xjtuecho/EBAZ4205/HW/ebaz4205/kicad/IO.kicad_sch

## KiCad design HW/ebaz4205/kicad/IO.kicad_sch (2021-02-16)

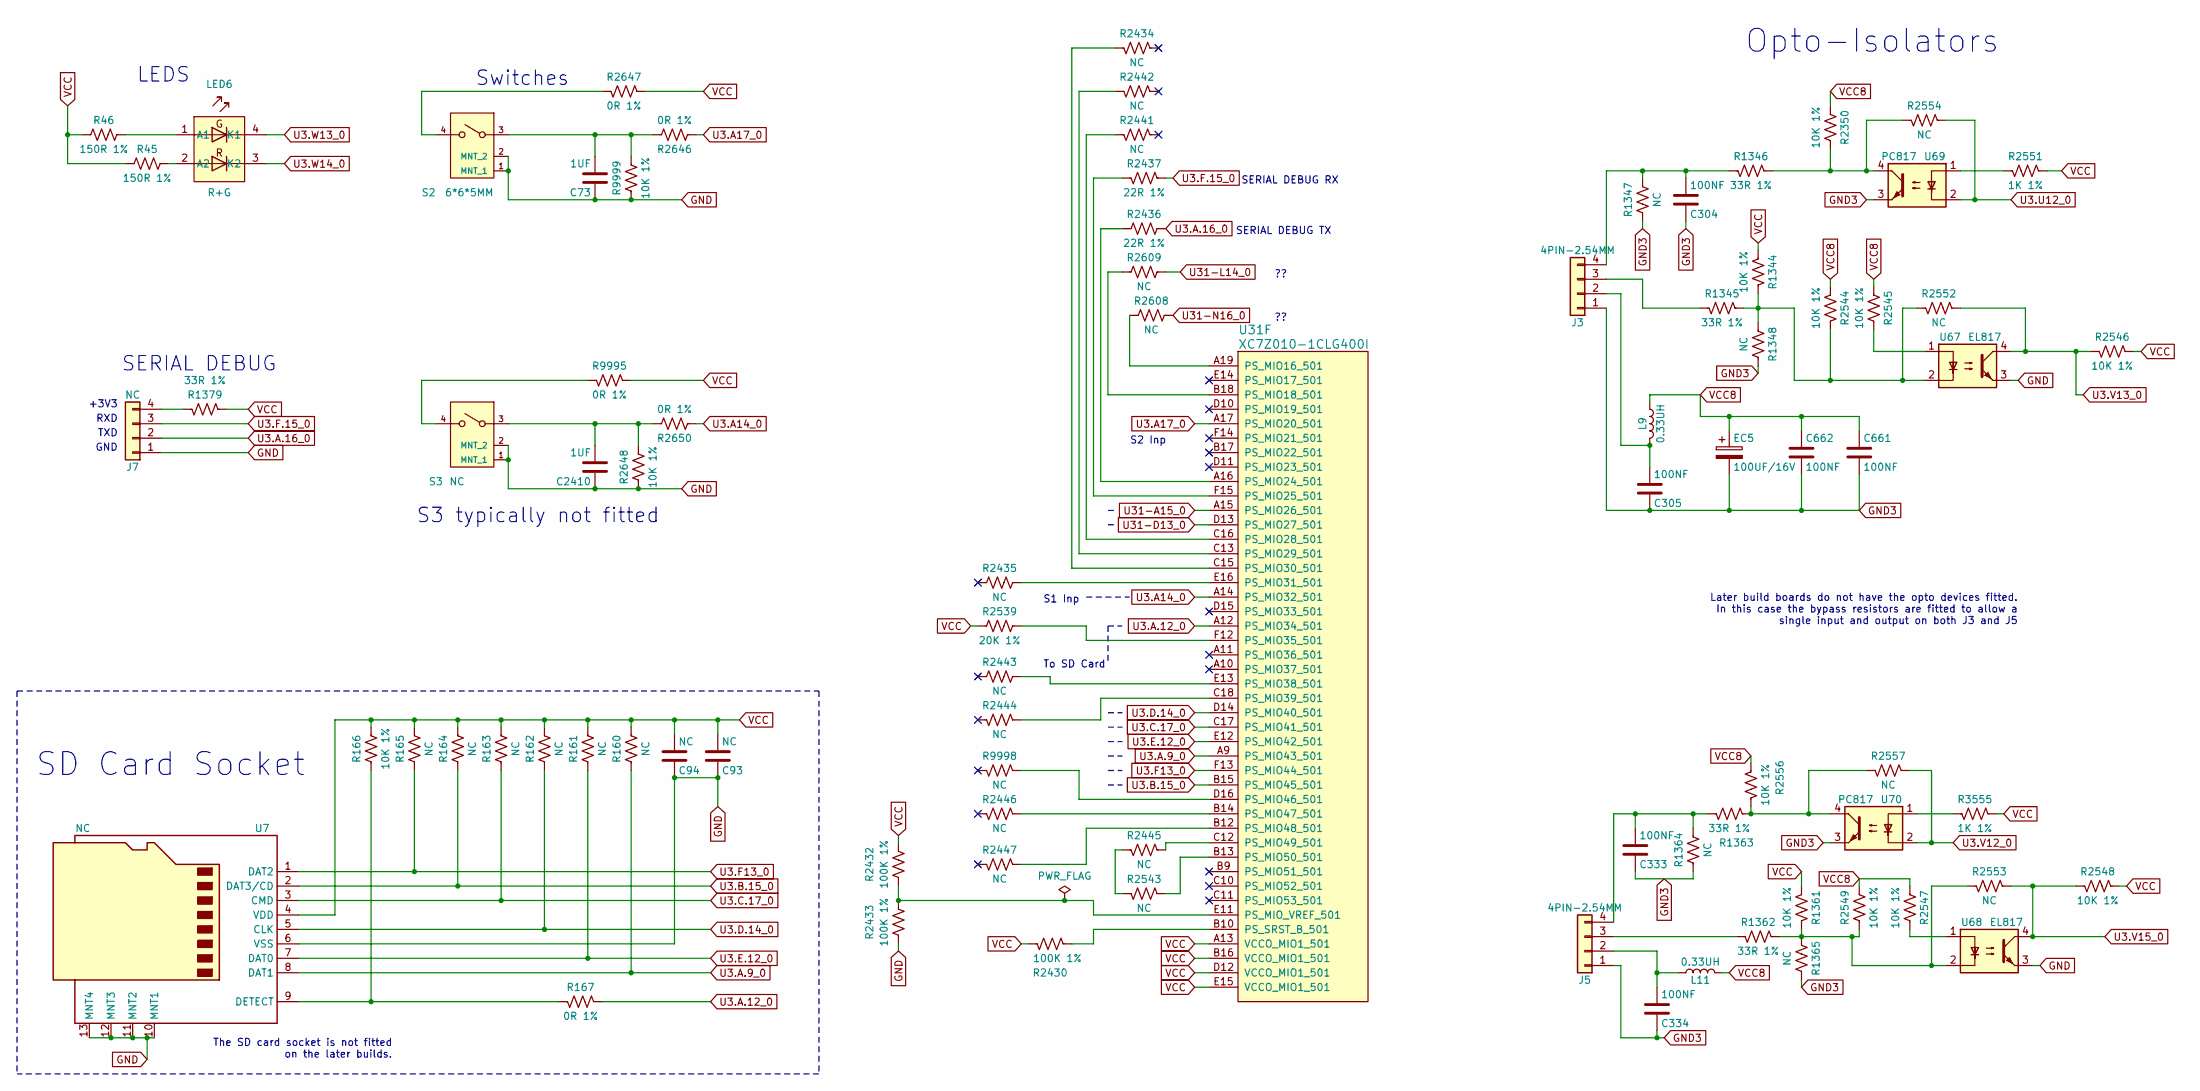
[picture p15: schematic IO.kicad_sch]

Parts:
C73, C2410: 1UF
C93, C94: NC
C304, C305, C333, C334, C661, C662: 100NF
EC5: 100UF/16V
J3, J5: 4PIN-2.54MM
J7: NC
L9, L11: 0.33UH
LED6: R+G
R45, R46: 150R 1%
R160, R161, R162, R163, R164, R165, R1347, R1348, R1364, R1365, R2434, R2435, R2441, R2442, R2443, R2444, R2445, R2446, R2447, R2543, R2552, R2553, R2554, R2557, R2608, R2609, R9998: NC
R166, R1344, R1361, R2350, R2544, R2545, R2546, R2547, R2548, R2549, R2556, R2648, R9999: 10K 1%
R167, R2646, R2647, R2650, R9995: 0R 1%
R1345, R1346, R1362, R1363, R1379: 33R 1%
R2430, R2432, R2433: 100K 1%
R2436, R2437: 22R 1%
R2539: 20K 1%
R2551, R3555: 1K 1%
S2: 6*6*5MM; voltage rating DC 24V; mouser part number 506-FSMRACD; digikey description SWITCH TACTILE SPST-NO 0.05A 24V
S3: NC; voltage rating DC 24V; mouser part number 506-FSMRACD; digikey description SWITCH TACTILE SPST-NO 0.05A 24V
U7: NC
U31: XC7Z010-1CLG400I
U67, U68: EL817
U69, U70: PC817

Connections:
GND: C73.1, C93.1, C94.1, C2410.1, J7.1, R2433.2, R2648.1, R9999.1, S2.1 (MNT_1), S2.2 (MNT_2), S3.1 (MNT_1), S3.2 (MNT_2), U7.6 (VSS), U7.10 (MNT1), U7.11 (MNT2), U7.12 (MNT3), U7.13 (MNT4), U67.3, U68.3
GND3: C304.1, C305.1, C333.1, C334.1, C661.1, C662.2, EC5.2, J3.1, J5.1, R1347.1, R1348.2, R1364.1, R1365.2, U69.3, U70.3
unnamed: C73.2, R2646.2, R9999.2, S2.3
unnamed: C304.2, J3.4, R1346.2, R1347.2
unnamed: C305.2, J3.2, L9.1
unnamed: C333.2, J5.4, R1363.2, R1364.2
unnamed: C334.2, J5.2, L11.1
unnamed: C2410.2, R2648.2, R2650.2, S3.3
unnamed: J3.3, R1345.2
unnamed: J5.3, R1362.2
unnamed: J7.4, R1379.2
unnamed: LED6.1 (A1), R46.2
unnamed: LED6.2 (A2), R45.2
unnamed: R166.1, R167.2, U7.9 (DETECT)
unnamed: R1344.1, R1345.1, R1348.1, R2544.1, R2552.2, U67.2
unnamed: R1346.1, R2350.2, R2554.2, U69.4
unnamed: R1361.1, R1362.1, R1365.1, R2549.1, R2553.2, U68.2
unnamed: R1363.1, R2556.2, R2557.2, U70.4
unnamed: R2430.1, U31.B10 (PS_SRST_B_501)
unnamed: R2432.1, R2433.1, U31.E11 (PS_MIO_VREF_501)
unnamed: R2434.2, U31.C15 (PS_MIO30_501)
unnamed: R2435.2, U31.E16 (PS_MIO31_501)
unnamed: R2436.1, U31.A16 (PS_MIO24_501)
unnamed: R2437.2, U31.F15 (PS_MIO25_501)
unnamed: R2441.2, U31.C16 (PS_MIO28_501)
unnamed: R2442.2, U31.C13 (PS_MIO29_501)
unnamed: R2443.2, U31.E13 (PS_MIO38_501)
unnamed: R2444.1, U31.C18 (PS_MIO39_501)
unnamed: R2445.1, U31.C12 (PS_MIO49_501)
unnamed: R2445.2, R2543.2
unnamed: R2446.1, U31.B14 (PS_MIO47_501)
unnamed: R2447.1, U31.B12 (PS_MIO48_501)
unnamed: R2539.2, U31.F12 (PS_MIO35_501)
unnamed: R2543.1, U31.B13 (PS_MIO50_501)
unnamed: R2545.2, U67.1
unnamed: R2547.2, U68.1
unnamed: R2551.2, U69.1
unnamed: R2608.1, U31.A19 (PS_MIO16_501)
unnamed: R2609.1, U31.B18 (PS_MIO18_501)
unnamed: R2647.2, S2.4
unnamed: R3555.2, U70.1
unnamed: R9995.2, S3.4
unnamed: R9998.1, U31.D16 (PS_MIO46_501)
U3.A14_0: R2650.1, U31.A14 (PS_MIO32_501)
U3.A17_0: R2646.1, U31.A17 (PS_MIO20_501)
U3.A.9_0: R160.1, U7.8 (DAT1), U31.A9 (PS_MIO43_501)
U3.A.12_0: R167.1, U31.A12 (PS_MIO34_501)
U3.A.16_0: J7.2, R2436.2
U3.B.15_0: R164.1, U7.2 (DAT3/CD), U31.B15 (PS_MIO45_501)
U3.C.17_0: R163.1, U7.3 (CMD), U31.C17 (PS_MIO41_501)
U3.D.14_0: R162.1, U7.5 (CLK), U31.D14 (PS_MIO40_501)
U3.E.12_0: R161.1, U7.7 (DAT0), U31.E12 (PS_MIO42_501)
U3.F13_0: R165.1, U7.1 (DAT2), U31.F13 (PS_MIO44_501)
U3.F.15_0: J7.3, R2437.1
U3.U12_0: R2554.1, U69.2
U3.V12_0: R2557.1, U70.2
U3.V13_0: R2546.2, R2552.1, U67.4
U3.V15_0: R2548.2, R2553.1, U68.4
U3.W13_0: LED6.4 (K1)
U3.W14_0: LED6.3 (K2)
U31-A15_0: U31.A15 (PS_MIO26_501)
U31-D13_0: U31.D13 (PS_MIO27_501)
U31-L14_0: R2609.2
U31-N16_0: R2608.2
VCC: C93.2, C94.2, R45.1, R46.1, R160.2, R161.2, R162.2, R163.2, R164.2, R165.2, R166.2, R1344.2, R1361.2, R1379.1, R2430.2, R2432.2, R2539.1, R2546.1, R2548.1, R2551.1, R2647.1, R3555.1, R9995.1, U7.4 (VDD), U31.A13 (VCCO_MIO1_501), U31.B16 (VCCO_MIO1_501), U31.D12 (VCCO_MIO1_501), U31.E15 (VCCO_MIO1_501)
VCC8: C661.2, C662.1, EC5.1, L9.2, L11.2, R2350.1, R2544.2, R2545.1, R2547.1, R2549.2, R2556.1

Notes on the sheet:
SD Card Socket
+3V3
RXD
TXD
GND
LEDS
SERIAL DEBUG
The SD card socket is not fitted on the later builds.
Switches
S3 typically not fitted
S1 Inp
To SD Card
S2 Inp
SERIAL DEBUG TX
SERIAL DEBUG RX
Opto-Isolators
Later build boards do not have the opto devices fitted. In this case the bypass resistors are fitted to allow a single input and output on both J3 and J5
