xjtuecho/EBAZ4205/HW/ebaz4205/kicad/Mem_Zynq.kicad_sch

## KiCad design HW/ebaz4205/kicad/Mem_Zynq.kicad_sch (2021-02-16)

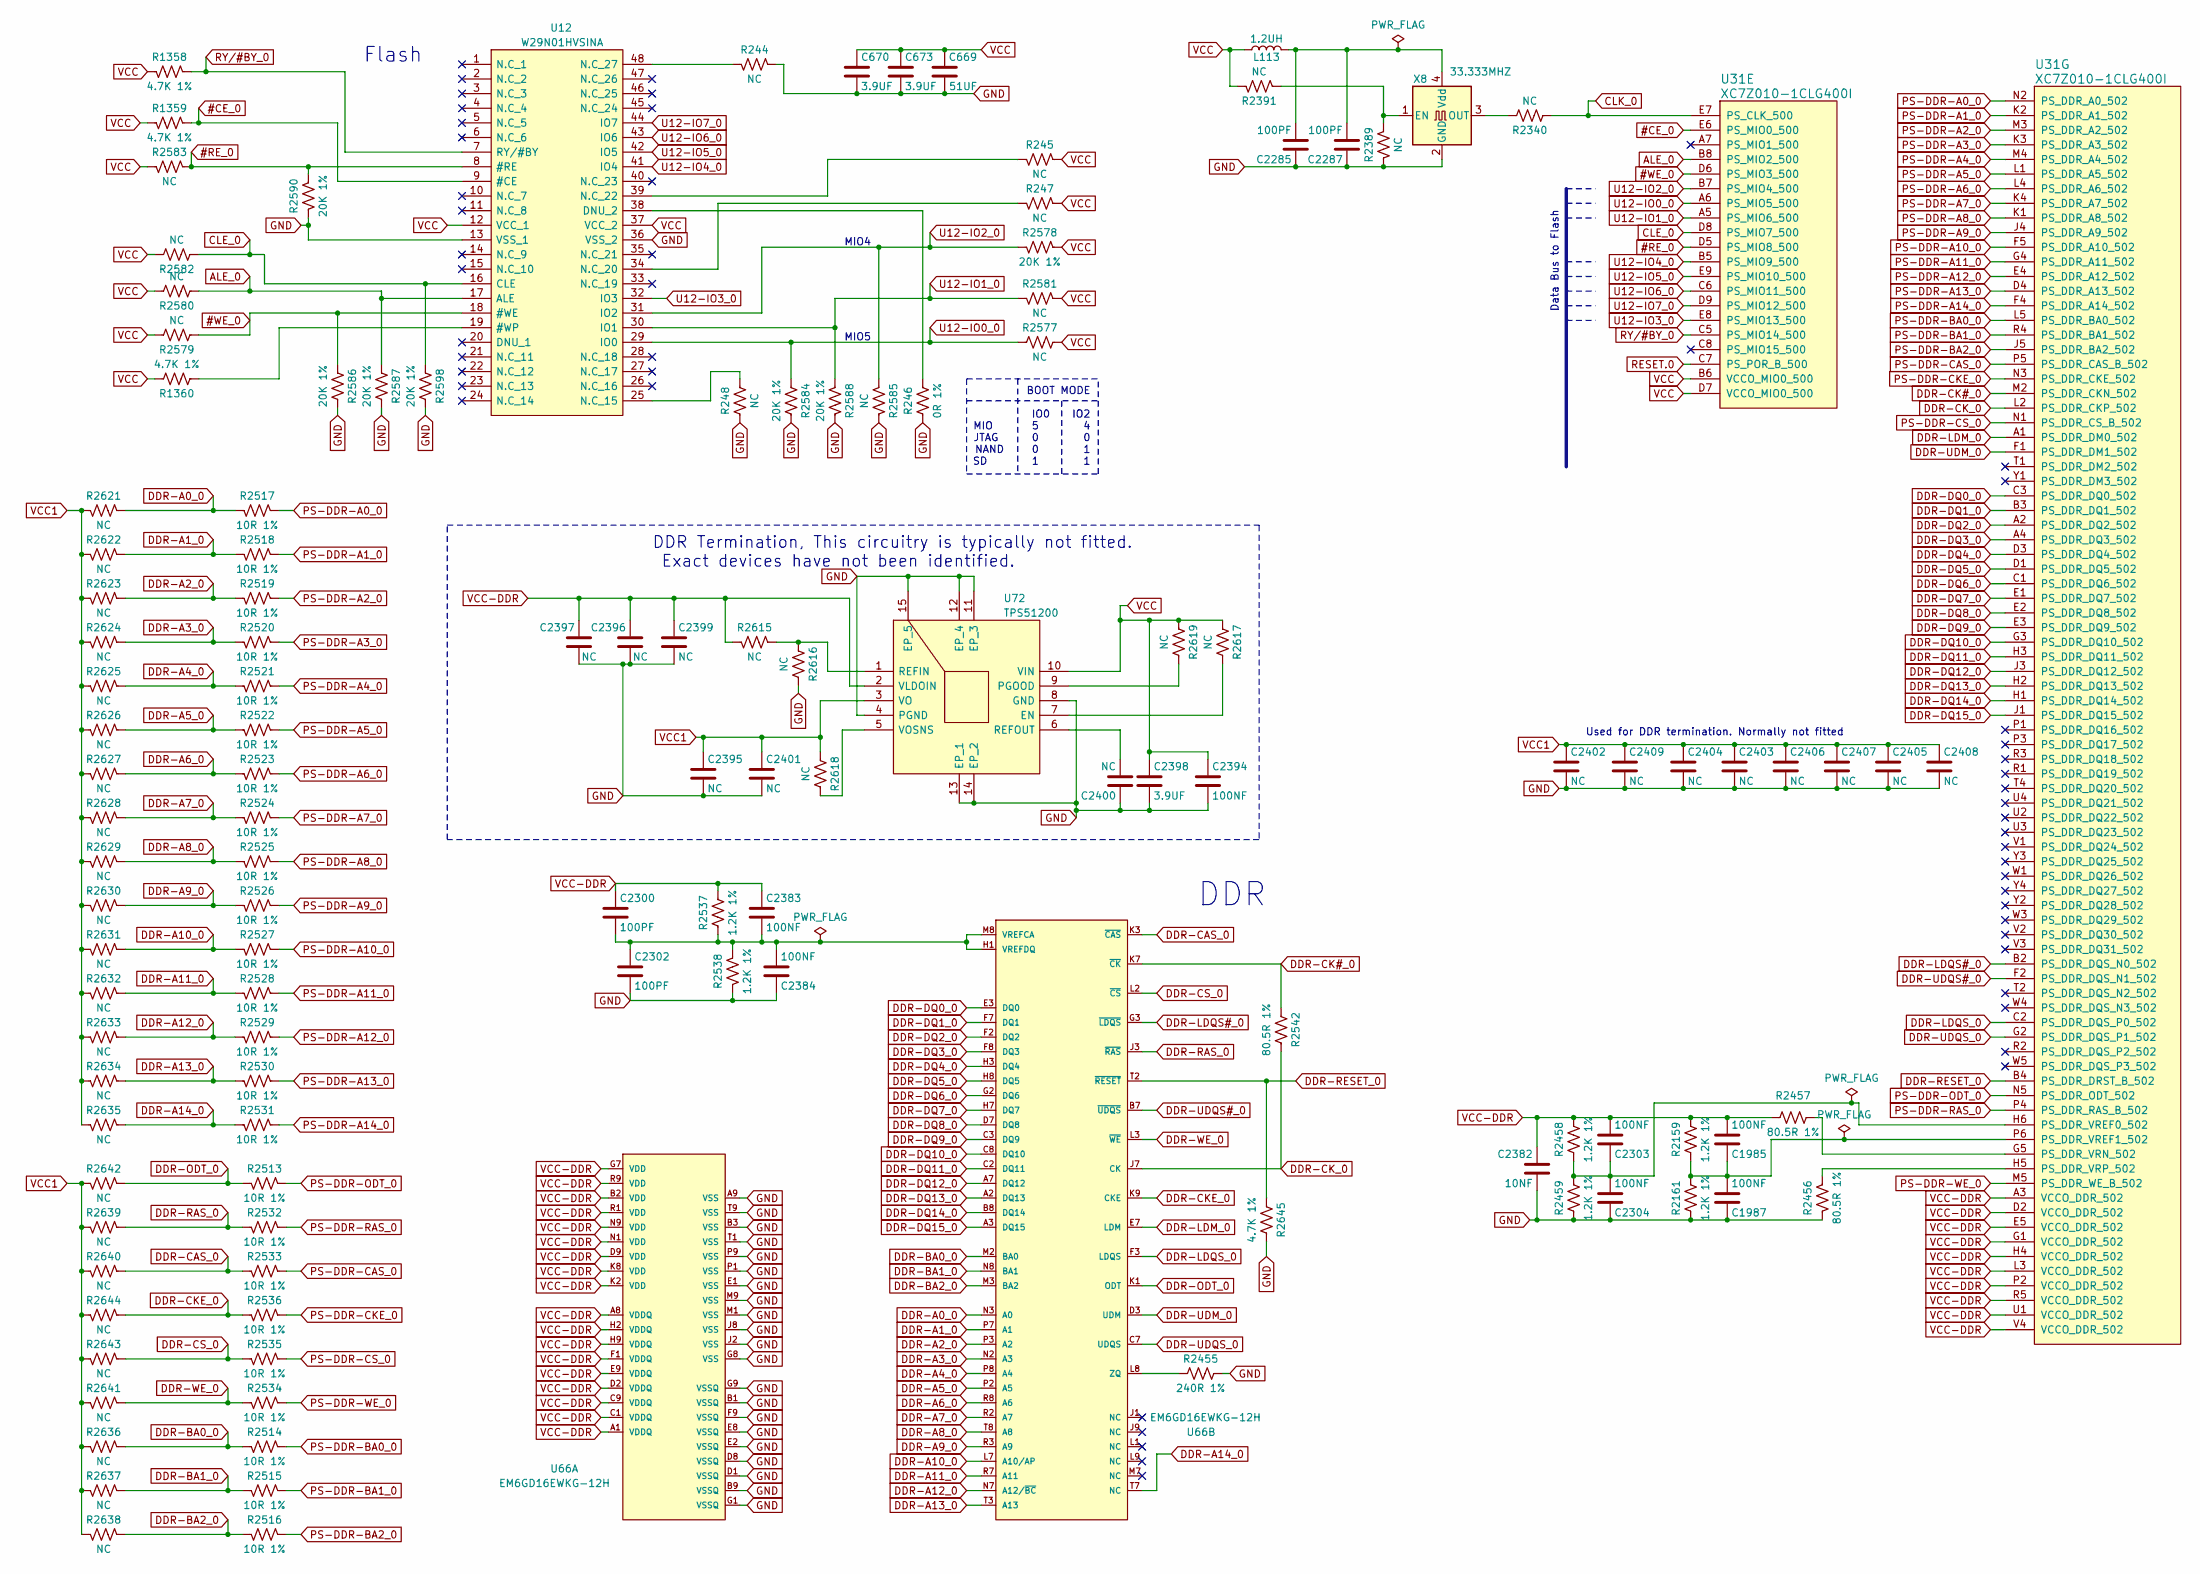
[picture p16: schematic Mem_Zynq.kicad_sch]

Parts:
C669: 51UF
C670, C673, C2398: 3.9UF
C1985, C1987, C2303, C2304, C2383, C2384, C2394: 100NF
C2285, C2287, C2300, C2302: 100PF
C2382: 10NF
C2395, C2396, C2397, C2399, C2400, C2401, C2402, C2403, C2404, C2405, C2406, C2407, C2408, C2409: NC
L113: 1.2UH
R244, R245, R247, R248, R2340, R2389, R2391, R2577, R2579, R2580, R2581, R2582, R2583, R2585, R2615, R2616, R2617, R2618, R2619, R2621, R2622, R2623, R2624, R2625, R2626, R2627, R2628, R2629, R2630, R2631, R2632, R2633, R2634, R2635, R2636, R2637, R2638, R2639, R2640, R2641, R2642, R2643, R2644: NC
R246: 0R 1%
R1358, R1359, R1360, R2645: 4.7K 1%
R2159, R2161, R2458, R2459, R2537, R2538: 1.2K 1%
R2455: 240R 1%
R2456, R2457, R2542: 80.5R 1%
R2513, R2514, R2515, R2516, R2517, R2518, R2519, R2520, R2521, R2522, R2523, R2524, R2525, R2526, R2527, R2528, R2529, R2530, R2531, R2532, R2533, R2534, R2535, R2536: 10R 1%
R2578, R2584, R2586, R2587, R2588, R2590, R2598: 20K 1%
U12: W29N01HVSINA; SOP50P2000X120-48N; Manufacturer_Part_Number W29N01HVSINA; Mouser Part Number 454-W29N01HVSINA
U31: XC7Z010-1CLG400I
U66: EM6GD16EWKG-12H; mouser part number 340-135814-TRAY; digikey description IC DRAM 2G PARALLEL 96FBGA
U72: TPS51200; Manufacturer_Part_Number TPS51200AQDRCRQ1; Mouser Part Number 595-TPS51200AQDRCRQ1
X8: 33.333MHZ

Connections:
#CE_0: R1359.1, U12.9 (#CE), U31.E6 (PS_MIO0_500)
#RE_0: R2583.1, R2590.1, U12.8 (#RE), U31.D5 (PS_MIO8_500)
#WE_0: R2579.1, R2586.1, U12.18 (#WE), U31.D6 (PS_MIO3_500)
ALE_0: R2580.1, R2587.1, U12.17 (ALE), U31.B8 (PS_MIO2_500)
CLE_0: R2582.1, R2598.1, U12.16 (CLE), U31.D8 (PS_MIO7_500)
CLK_0: R2340.1, U31.E7 (PS_CLK_500)
DDR-A0_0: R2517.2, R2621.1, U66.N3 (A0)
DDR-A1_0: R2518.2, R2622.1, U66.P7 (A1)
DDR-A2_0: R2519.2, R2623.1, U66.P3 (A2)
DDR-A3_0: R2520.2, R2624.1, U66.N2 (A3)
DDR-A4_0: R2521.2, R2625.1, U66.P8 (A4)
DDR-A5_0: R2522.2, R2626.1, U66.P2 (A5)
DDR-A6_0: R2523.2, R2627.1, U66.R8 (A6)
DDR-A7_0: R2524.2, R2628.1, U66.R2 (A7)
DDR-A8_0: R2525.2, R2629.1, U66.T8 (A8)
DDR-A9_0: R2526.2, R2630.1, U66.R3 (A9)
DDR-A10_0: R2527.2, R2631.1, U66.L7 (A10/AP)
DDR-A11_0: R2528.2, R2632.1, U66.R7 (A11)
DDR-A12_0: R2529.2, R2633.1, U66.N7 (A12/~BC~)
DDR-A13_0: R2530.2, R2634.1, U66.T3 (A13)
DDR-A14_0: R2531.2, R2635.1, U66.T7 (NC)
DDR-BA0_0: R2514.2, R2636.1, U66.M2 (BA0)
DDR-BA1_0: R2515.2, R2637.1, U66.N8 (BA1)
DDR-BA2_0: R2516.2, R2638.1, U66.M3 (BA2)
DDR-CAS_0: R2533.2, R2640.1, U66.K3 (~CAS~)
DDR-CK#_0: R2542.1, U31.M2 (PS_DDR_CKN_502), U66.K7 (~CK~)
DDR-CKE_0: R2536.2, R2644.1, U66.K9 (CKE)
DDR-CK_0: R2542.2, U31.L2 (PS_DDR_CKP_502), U66.J7 (CK)
DDR-CS_0: R2535.2, R2643.1, U66.L2 (~CS~)
DDR-DQ0_0: U31.C3 (PS_DDR_DQ0_502), U66.E3 (DQ0)
DDR-DQ1_0: U31.B3 (PS_DDR_DQ1_502), U66.F7 (DQ1)
DDR-DQ2_0: U31.A2 (PS_DDR_DQ2_502), U66.F2 (DQ2)
DDR-DQ3_0: U31.A4 (PS_DDR_DQ3_502), U66.F8 (DQ3)
DDR-DQ4_0: U31.D3 (PS_DDR_DQ4_502), U66.H3 (DQ4)
DDR-DQ5_0: U31.D1 (PS_DDR_DQ5_502), U66.H8 (DQ5)
DDR-DQ6_0: U31.C1 (PS_DDR_DQ6_502), U66.G2 (DQ6)
DDR-DQ7_0: U31.E1 (PS_DDR_DQ7_502), U66.H7 (DQ7)
DDR-DQ8_0: U31.E2 (PS_DDR_DQ8_502), U66.D7 (DQ8)
DDR-DQ9_0: U31.E3 (PS_DDR_DQ9_502), U66.C3 (DQ9)
DDR-DQ10_0: U31.G3 (PS_DDR_DQ10_502), U66.C8 (DQ10)
DDR-DQ11_0: U31.H3 (PS_DDR_DQ11_502), U66.C2 (DQ11)
DDR-DQ12_0: U31.J3 (PS_DDR_DQ12_502), U66.A7 (DQ12)
DDR-DQ13_0: U31.H2 (PS_DDR_DQ13_502), U66.A2 (DQ13)
DDR-DQ14_0: U31.H1 (PS_DDR_DQ14_502), U66.B8 (DQ14)
DDR-DQ15_0: U31.J1 (PS_DDR_DQ15_502), U66.A3 (DQ15)
DDR-LDM_0: U31.A1 (PS_DDR_DM0_502), U66.E7 (LDM)
DDR-LDQS#_0: U31.B2 (PS_DDR_DQS_N0_502), U66.G3 (~LDQS~)
DDR-LDQS_0: U31.C2 (PS_DDR_DQS_P0_502), U66.F3 (LDQS)
DDR-ODT_0: R2513.2, R2642.1, U66.K1 (ODT)
DDR-RAS_0: R2532.2, R2639.1, U66.J3 (~RAS~)
DDR-RESET_0: R2645.1, U31.B4 (PS_DDR_DRST_B_502), U66.T2 (~RESET~)
DDR-UDM_0: U31.F1 (PS_DDR_DM1_502), U66.D3 (UDM)
DDR-UDQS#_0: U31.F2 (PS_DDR_DQS_N1_502), U66.B7 (~UDQS~)
DDR-UDQS_0: U31.G2 (PS_DDR_DQS_P1_502), U66.C7 (UDQS)
DDR-WE_0: R2534.2, R2641.1, U66.L3 (~WE~)
GND: C669.1, C670.2, C673.2, C1987.1, C2285.1, C2287.1, C2302.2, C2304.1, C2382.2, C2384.1, C2394.2, C2395.2, C2396.1, C2397.1, C2398.2, C2399.2, C2400.1, C2401.2, C2402.1, C2403.2, C2404.2, C2405.2, C2406.2, C2407.2, C2408.2, C2409.2, R244.1, R246.1, R248.1, R2161.1, R2389.2, R2455.2, R2456.2, R2459.1, R2538.2, R2584.2, R2585.1, R2586.2, R2587.2, R2588.1, R2590.2, R2598.2, R2616.2, R2645.2, U12.13 (VSS_1), U12.36 (VSS_2), U66.A9 (VSS), U66.B1 (VSSQ), U66.B3 (VSS), U66.B9 (VSSQ), U66.D1 (VSSQ), U66.D8 (VSSQ), U66.E1 (VSS), U66.E2 (VSSQ), U66.E8 (VSSQ), U66.F9 (VSSQ), U66.G1 (VSSQ), U66.G8 (VSS), U66.G9 (VSSQ), U66.J2 (VSS), U66.J8 (VSS), U66.M1 (VSS), U66.M9 (VSS), U66.P1 (VSS), U66.P9 (VSS), U66.T1 (VSS), U66.T9 (VSS), U72.4 (PGND), U72.8 (GND), U72.11 (EP_3), U72.12 (EP_4), U72.13 (EP_1), U72.14 (EP_2), U72.15 (EP_5), X8.2 (GND)
unnamed: C1985.1, C1987.2, R2159.1, R2161.2, U31.P6 (PS_DDR_VREF1_502)
unnamed: C2285.2, C2287.2, L113.2, X8.4 (Vdd)
unnamed: C2300.2, C2302.1, C2383.2, C2384.2, R2537.1, R2538.1, U66.H1 (VREFDQ), U66.M8 (VREFCA)
unnamed: C2303.1, C2304.2, R2458.1, R2459.2, U31.H6 (PS_DDR_VREF0_502)
unnamed: C2400.2, U72.6 (REFOUT)
unnamed: R244.2, U12.48 (N.C_27)
unnamed: R245.2, U12.39 (N.C_22)
unnamed: R246.2, U12.38 (DNU_2)
unnamed: R247.2, U12.34 (N.C_20)
unnamed: R248.2, U12.25 (N.C_15)
unnamed: R1360.1, U12.19 (#WP)
unnamed: R2340.2, X8.3 (OUT)
unnamed: R2389.1, R2391.2, X8.1 (EN)
unnamed: R2455.1, U66.L8 (ZQ)
unnamed: R2456.1, U31.H5 (PS_DDR_VRP_502)
unnamed: R2457.2, U31.G5 (PS_DDR_VRN_502)
unnamed: R2615.1, R2616.1, U72.1 (REFIN)
unnamed: R2617.2, U72.7 (EN)
unnamed: R2618.2, U72.5 (VOSNS)
unnamed: R2619.2, U72.9 (PGOOD)
PS-DDR-A0_0: R2517.1, U31.N2 (PS_DDR_A0_502)
PS-DDR-A1_0: R2518.1, U31.K2 (PS_DDR_A1_502)
PS-DDR-A2_0: R2519.1, U31.M3 (PS_DDR_A2_502)
PS-DDR-A3_0: R2520.1, U31.K3 (PS_DDR_A3_502)
PS-DDR-A4_0: R2521.1, U31.M4 (PS_DDR_A4_502)
PS-DDR-A5_0: R2522.1, U31.L1 (PS_DDR_A5_502)
PS-DDR-A6_0: R2523.1, U31.L4 (PS_DDR_A6_502)
PS-DDR-A7_0: R2524.1, U31.K4 (PS_DDR_A7_502)
PS-DDR-A8_0: R2525.1, U31.K1 (PS_DDR_A8_502)
PS-DDR-A9_0: R2526.1, U31.J4 (PS_DDR_A9_502)
PS-DDR-A10_0: R2527.1, U31.F5 (PS_DDR_A10_502)
PS-DDR-A11_0: R2528.1, U31.G4 (PS_DDR_A11_502)
PS-DDR-A12_0: R2529.1, U31.E4 (PS_DDR_A12_502)
PS-DDR-A13_0: R2530.1, U31.D4 (PS_DDR_A13_502)
PS-DDR-A14_0: R2531.1, U31.F4 (PS_DDR_A14_502)
PS-DDR-BA0_0: R2514.1, U31.L5 (PS_DDR_BA0_502)
PS-DDR-BA1_0: R2515.1, U31.R4 (PS_DDR_BA1_502)
PS-DDR-BA2_0: R2516.1, U31.J5 (PS_DDR_BA2_502)
PS-DDR-CAS_0: R2533.1, U31.P5 (PS_DDR_CAS_B_502)
PS-DDR-CKE_0: R2536.1, U31.N3 (PS_DDR_CKE_502)
PS-DDR-CS_0: R2535.1, U31.N1 (PS_DDR_CS_B_502)
PS-DDR-ODT_0: R2513.1, U31.N5 (PS_DDR_ODT_502)
PS-DDR-RAS_0: R2532.1, U31.P4 (PS_DDR_RAS_B_502)
PS-DDR-WE_0: R2534.1, U31.M5 (PS_DDR_WE_B_502)
RESET.0: U31.C7 (PS_POR_B_500)
RY/#BY_0: R1358.1, U12.7 (RY/#BY), U31.C5 (PS_MIO14_500)
U12-IO0_0: R2577.1, R2584.1, U12.29 (IO0), U31.A6 (PS_MIO5_500)
U12-IO1_0: R2581.2, R2588.2, U12.30 (IO1), U31.A5 (PS_MIO6_500)
U12-IO2_0: R2578.2, R2585.2, U12.31 (IO2), U31.B7 (PS_MIO4_500)
U12-IO3_0: U12.32 (IO3), U31.E8 (PS_MIO13_500)
U12-IO4_0: U12.41 (IO4), U31.B5 (PS_MIO9_500)
U12-IO5_0: U12.42 (IO5), U31.E9 (PS_MIO10_500)
U12-IO6_0: U12.43 (IO6), U31.C6 (PS_MIO11_500)
U12-IO7_0: U12.44 (IO7), U31.D9 (PS_MIO12_500)
VCC: C669.2, C670.1, C673.1, C2394.1, C2398.1, L113.1, R245.1, R247.1, R1358.2, R1359.2, R1360.2, R2391.1, R2577.2, R2578.1, R2579.2, R2580.2, R2581.1, R2582.2, R2583.2, R2617.1, R2619.1, U12.12 (VCC_1), U12.37 (VCC_2), U31.B6 (VCCO_MIO0_500), U31.D7 (VCCO_MIO0_500), U72.10 (VIN)
VCC1: C2395.1, C2401.1, C2402.2, C2403.1, C2404.1, C2405.1, C2406.1, C2407.1, C2408.1, C2409.1, R2618.1, R2621.2, R2622.2, R2623.2, R2624.2, R2625.2, R2626.2, R2627.2, R2628.2, R2629.2, R2630.2, R2631.2, R2632.2, R2633.2, R2634.2, R2635.2, R2636.2, R2637.2, R2638.2, R2639.2, R2640.2, R2641.2, R2642.2, R2643.2, R2644.2, U72.3 (VO)
VCC-DDR: C1985.2, C2300.1, C2303.2, C2382.1, C2383.1, C2396.2, C2397.2, C2399.1, R2159.2, R2457.1, R2458.2, R2537.2, R2615.2, U31.A3 (VCCO_DDR_502), U31.D2 (VCCO_DDR_502), U31.E5 (VCCO_DDR_502), U31.G1 (VCCO_DDR_502), U31.H4 (VCCO_DDR_502), U31.L3 (VCCO_DDR_502), U31.P2 (VCCO_DDR_502), U31.R5 (VCCO_DDR_502), U31.U1 (VCCO_DDR_502), U31.V4 (VCCO_DDR_502), U66.A1 (VDDQ), U66.A8 (VDDQ), U66.B2 (VDD), U66.C1 (VDDQ), U66.C9 (VDDQ), U66.D2 (VDDQ), U66.D9 (VDD), U66.E9 (VDDQ), U66.F1 (VDDQ), U66.G7 (VDD), U66.H2 (VDDQ), U66.H9 (VDDQ), U66.K2 (VDD), U66.K8 (VDD), U66.N1 (VDD), U66.N9 (VDD), U66.R1 (VDD), U66.R9 (VDD), U72.2 (VLDOIN)

Notes on the sheet:
Flash
DDR Termination, This circuitry is typically not fitted. Exact devices have not been identified.
MIO4
MIO5
BOOT MODE IO0 IO2 MIO 5 4 JTAG 0 0 NAND 0 1 SD 1 1
DDR
Data Bus to Flash
Used for DDR termination. Normally not fitted
