xjtuecho/EBAZ4205/HW/ebaz4205/kicad/Phy-Sun.kicad_sch

## KiCad design HW/ebaz4205/kicad/Phy-Sun.kicad_sch (2021-02-16)

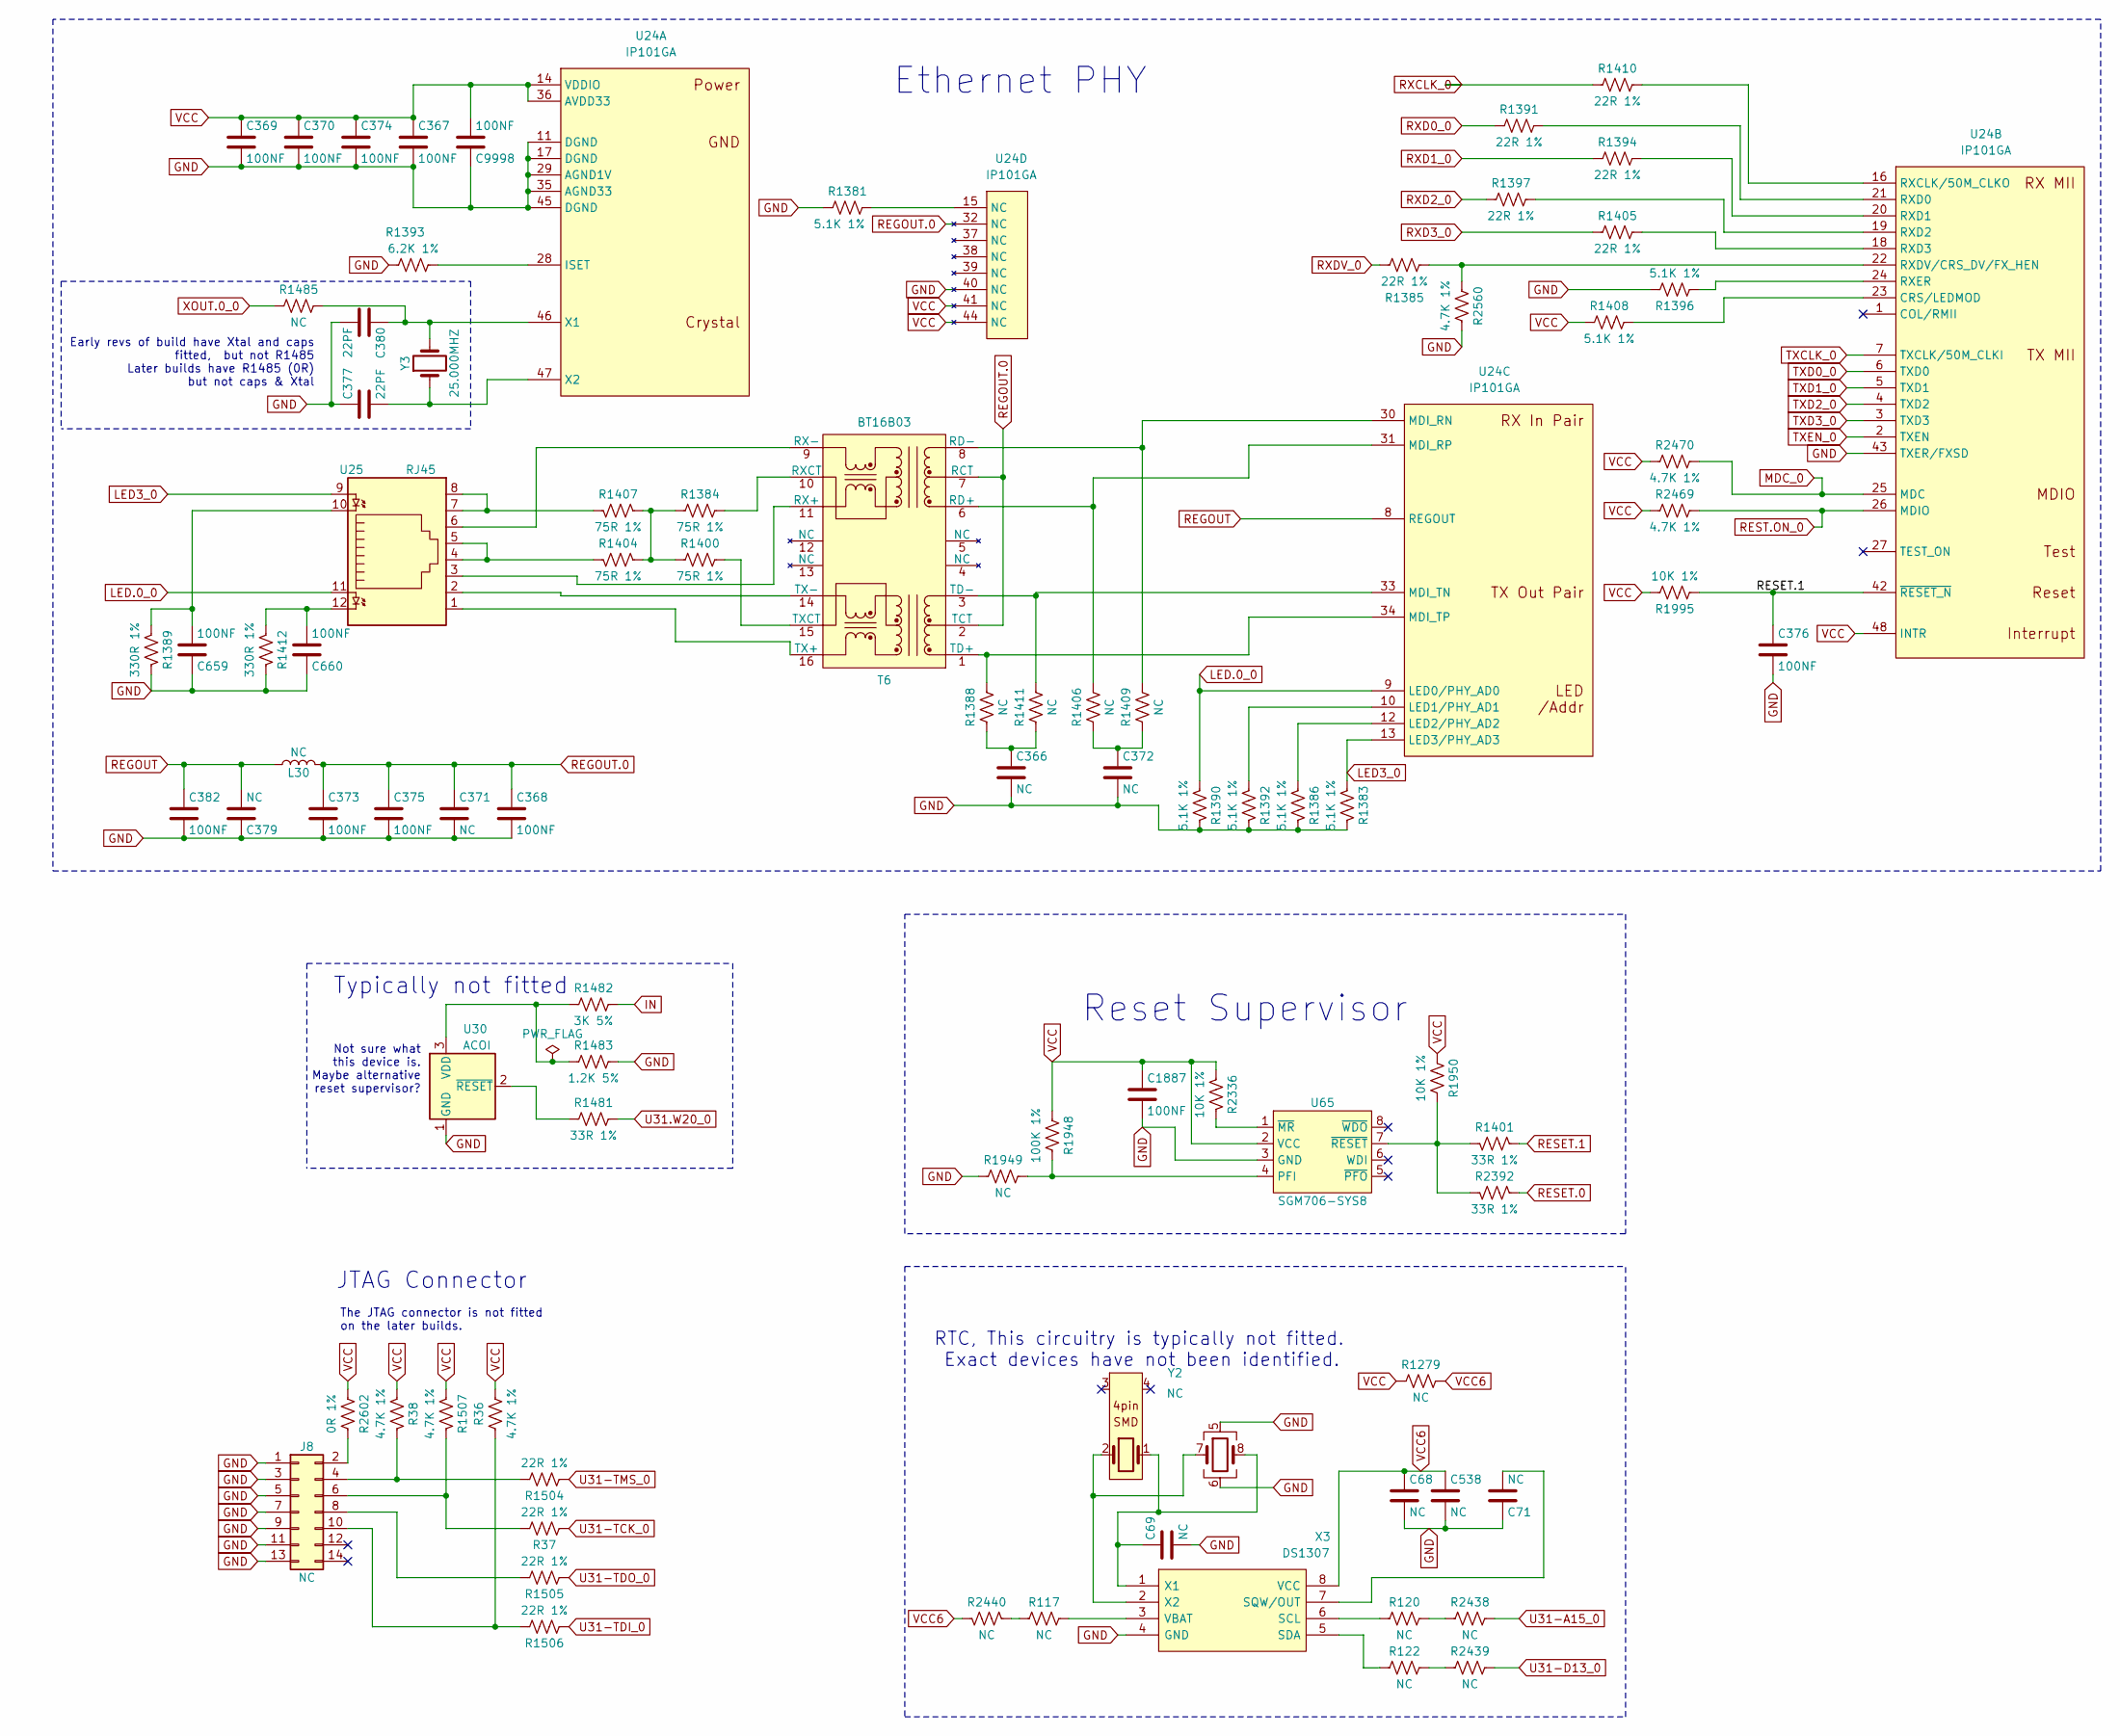
[picture p17: schematic Phy-Sun.kicad_sch]

Parts:
C68, C69, C71, C366, C371, C372, C379, C538: NC
C367, C368, C369, C370, C373, C374, C375, C376, C382, C659, C660, C1887, C9998: 100NF
C377, C380: 22PF
J8: NC
L30: NC
R36, R38, R1507, R2469, R2470, R2560: 4.7K 1%
R37, R1385, R1391, R1394, R1397, R1405, R1410, R1504, R1505, R1506: 22R 1%
R117, R120, R122, R1279, R1388, R1406, R1409, R1411, R1485, R1949, R2438, R2439, R2440: NC
R1381, R1383, R1386, R1390, R1392, R1396, R1408: 5.1K 1%
R1384, R1400, R1404, R1407: 75R 1%
R1389, R1412: 330R 1%
R1393: 6.2K 1%
R1401, R1481, R2392: 33R 1%
R1482: 3K 5%
R1483: 1.2K 5%
R1948: 100K 1%
R1950, R1995, R2336: 10K 1%
R2602: 0R 1%
T6: BT16B03
U24: IP101GA
U25: RJ45
U30: ACOI
U65: SGM706-SYS8
X3: DS1307; Manufacturer_Part_Number DS1307Z+; Mouser Part Number 700-DS1307Z
Y2: NC
Y3: 25.000MHZ

Connections:
GND: C68.2, C69.2, C71.1, C366.2, C367.2, C368.2, C369.2, C370.2, C371.2, C372.2, C373.2, C374.2, C375.2, C376.2, C377.1, C379.1, C380.2, C382.2, C538.2, C659.1, C660.1, C1887.2, C9998.1, J8.1, J8.3, J8.5, J8.7, J8.9, J8.11, J8.13, R1381.1, R1383.1, R1386.1, R1389.1, R1390.1, R1392.1, R1393.2, R1396.2, R1412.1, R1483.2, R1949.1, R2560.2, U24.11 (DGND), U24.17 (DGND), U24.29 (AGND1V), U24.35 (AGND33), U24.40 (NC), U24.43 (TXER/FXSD), U24.45 (DGND), U30.1 (GND), U65.3 (GND), X3.4 (GND), Y2.5, Y2.6
IN: R1482.2
LED3_0: R1383.2, U24.13 (LED3/PHY_AD3), U25.9
LED.0_0: R1390.2, U24.9 (LED0/PHY_AD0), U25.11
MDC_0: R2470.2, U24.25 (MDC)
unnamed: C69.1, X3.1 (X1), Y2.1, Y2.8
unnamed: C71.2, X3.7 (SQW/OUT)
unnamed: C366.1, R1388.1, R1411.1
unnamed: C372.1, R1406.1, R1409.1
unnamed: C377.2, U24.47 (X2), Y3.1
unnamed: C380.1, R1485.2, U24.46 (X1), Y3.2
unnamed: C659.2, R1389.2, U25.10
unnamed: C660.2, R1412.2, U25.12
unnamed: J8.2, R2602.2
unnamed: J8.4, R38.1, R1504.2
unnamed: J8.6, R37.2, R1507.1
unnamed: J8.8, R1505.2
unnamed: J8.10, R36.1, R1506.2
unnamed: R117.1, R2440.1
unnamed: R117.2, X3.3 (VBAT)
unnamed: R120.1, X3.6 (SCL)
unnamed: R120.2, R2438.1
unnamed: R122.1, X3.5 (SDA)
unnamed: R122.2, R2439.1
unnamed: R1381.2, U24.15 (NC)
unnamed: R1384.1, R1400.1, R1404.1, R1407.1
unnamed: R1384.2, T6.10 (RXCT)
unnamed: R1385.2, R2560.1, U24.22 (RXDV/CRS_DV/FX_HEN)
unnamed: R1386.2, U24.12 (LED2/PHY_AD2)
unnamed: R1388.2, T6.1 (TD+), U24.34 (MDI_TP)
unnamed: R1391.2, U24.21 (RXD0)
unnamed: R1392.2, U24.10 (LED1/PHY_AD1)
unnamed: R1393.1, U24.28 (ISET)
unnamed: R1394.2, U24.20 (RXD1)
unnamed: R1396.1, U24.24 (RXER)
unnamed: R1397.2, U24.19 (RXD2)
unnamed: R1400.2, T6.15 (TXCT)
unnamed: R1401.2, R1950.2, R2392.2, U65.7 (~RESET)
unnamed: R1404.2, U25.4, U25.5
unnamed: R1405.2, U24.18 (RXD3)
unnamed: R1406.2, T6.6 (RD+), U24.31 (MDI_RP)
unnamed: R1407.2, U25.7, U25.8
unnamed: R1408.2, U24.23 (CRS/LEDMOD)
unnamed: R1409.2, T6.8 (RD-), U24.30 (MDI_RN)
unnamed: R1410.2, U24.16 (RXCLK/50M_CLKO)
unnamed: R1411.2, T6.3 (TD-), U24.33 (MDI_TN)
unnamed: R1481.1, U30.2 (~RESET)
unnamed: R1482.1, R1483.1, U30.3 (VDD)
unnamed: R1948.2, R1949.2, U65.4 (PFI)
unnamed: R2336.1, U65.1 (~MR)
unnamed: T6.9 (RX-), U25.6
unnamed: T6.11 (RX+), U25.3
unnamed: T6.14 (TX-), U25.2
unnamed: T6.16 (TX+), U25.1
unnamed: X3.2 (X2), Y2.2, Y2.7
REGOUT: C379.2, C382.1, L30.2, U24.8 (REGOUT)
REGOUT.0: C368.1, C371.1, C373.1, C375.1, L30.1, T6.2 (TCT), T6.7 (RCT), U24.32 (NC)
RESET.0: R2392.1
RESET.1: C376.1, R1401.1, R1995.1, U24.42 (~RESET_N)
REST.ON_0: R2469.2, U24.26 (MDIO)
RXCLK_0: R1410.1
RXD0_0: R1391.1
RXD1_0: R1394.1
RXD2_0: R1397.1
RXD3_0: R1405.1
RXDV_0: R1385.1
TXCLK_0: U24.7 (TXCLK/50M_CLKI)
TXD0_0: U24.6 (TXD0)
TXD1_0: U24.5 (TXD1)
TXD2_0: U24.4 (TXD2)
TXD3_0: U24.3 (TXD3)
TXEN_0: U24.2 (TXEN)
U31-A15_0: R2438.2
U31-D13_0: R2439.2
U31-TCK_0: R37.1
U31-TDI_0: R1506.1
U31-TDO_0: R1505.1
U31-TMS_0: R1504.1
U31.W20_0: R1481.2
VCC: C367.1, C369.1, C370.1, C374.1, C1887.1, C9998.2, R36.2, R38.2, R1279.1, R1408.1, R1507.2, R1948.1, R1950.1, R1995.2, R2336.2, R2469.1, R2470.1, R2602.1, U24.14 (VDDIO), U24.36 (AVDD33), U24.41 (NC), U24.44 (NC), U24.48 (INTR), U65.2 (VCC)
VCC6: C68.1, C538.1, R1279.2, R2440.2, X3.8 (VCC)
XOUT.0_0: R1485.1

Notes on the sheet:
Early revs of build have Xtal and caps fitted, but not R1485 Later builds have R1485 (0R) but not caps & Xtal
The JTAG connector is not fitted on the later builds.
Not sure what this device is. Maybe alternative reset supervisor?
JTAG Connector
Typically not fitted
Ethernet PHY
RTC, This circuitry is typically not fitted. Exact devices have not been identified.
Reset Supervisor
