xjtuecho/EBAZ4205/HW/ebaz4205/kicad/Zynq_IO.kicad_sch

## KiCad design HW/ebaz4205/kicad/Zynq_IO.kicad_sch (2021-02-16)

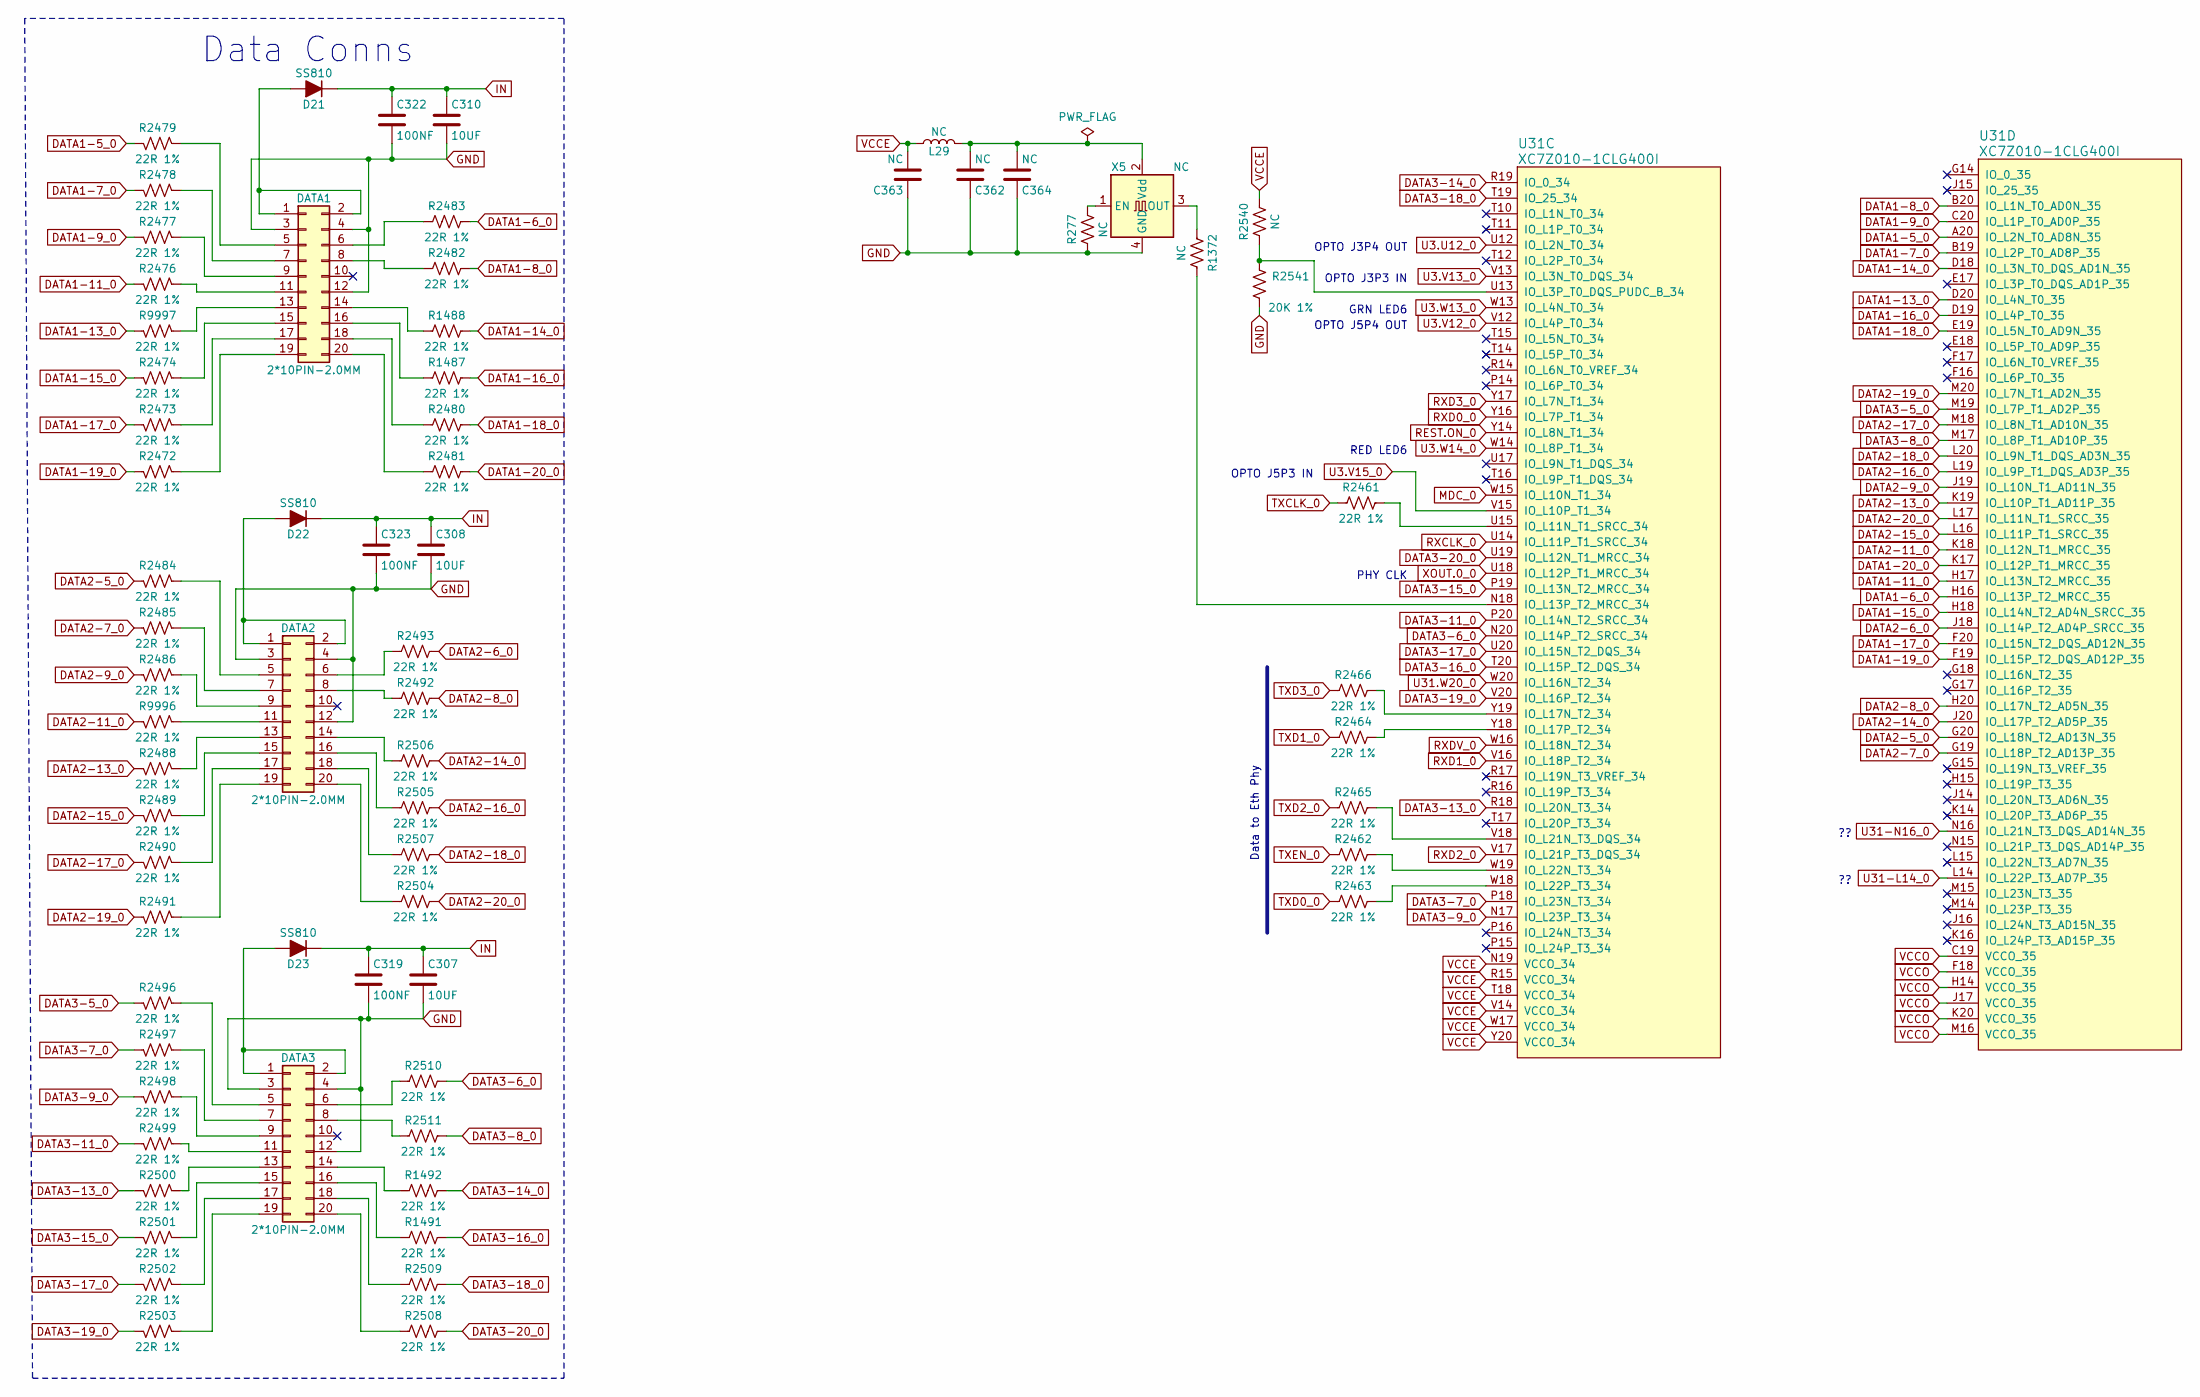
[picture p18: schematic Zynq_IO.kicad_sch]

Parts:
C307, C308, C310: 10UF
C319, C322, C323: 100NF
C362, C363, C364: NC
D21, D22, D23: SS810
DATA1, DATA2, DATA3: 2*10PIN-2.0MM
L29: NC
R277, R1372, R2540: NC
R1487, R1488, R1491, R1492, R2461, R2462, R2463, R2464, R2465, R2466, R2472, R2473, R2474, R2476, R2477, R2478, R2479, R2480, R2481, R2482, R2483, R2484, R2485, R2486, R2488, R2489, R2490, R2491, R2492, R2493, R2496, R2497, R2498, R2499, R2500, R2501, R2502, R2503, R2504, R2505, R2506, R2507, R2508, R2509, R2510, R2511, R9996, R9997: 22R 1%
R2541: 20K 1%
U31: XC7Z010-1CLG400I
X5: NC

Connections:
DATA1-5_0: R2479.2, U31.A20 (IO_L2N_T0_AD8N_35)
DATA1-6_0: R2483.2, U31.H16 (IO_L13P_T2_MRCC_35)
DATA1-7_0: R2478.2, U31.B19 (IO_L2P_T0_AD8P_35)
DATA1-8_0: R2482.2, U31.B20 (IO_L1N_T0_AD0N_35)
DATA1-9_0: R2477.2, U31.C20 (IO_L1P_T0_AD0P_35)
DATA1-11_0: R2476.2, U31.H17 (IO_L13N_T2_MRCC_35)
DATA1-13_0: R9997.2, U31.D20 (IO_L4N_T0_35)
DATA1-14_0: R1488.2, U31.D18 (IO_L3N_T0_DQS_AD1N_35)
DATA1-15_0: R2474.2, U31.H18 (IO_L14N_T2_AD4N_SRCC_35)
DATA1-16_0: R1487.2, U31.D19 (IO_L4P_T0_35)
DATA1-17_0: R2473.2, U31.F20 (IO_L15N_T2_DQS_AD12N_35)
DATA1-18_0: R2480.2, U31.E19 (IO_L5N_T0_AD9N_35)
DATA1-19_0: R2472.2, U31.F19 (IO_L15P_T2_DQS_AD12P_35)
DATA1-20_0: R2481.2, U31.K17 (IO_L12P_T1_MRCC_35)
DATA2-5_0: R2484.2, U31.G20 (IO_L18N_T2_AD13N_35)
DATA2-6_0: R2493.2, U31.J18 (IO_L14P_T2_AD4P_SRCC_35)
DATA2-7_0: R2485.2, U31.G19 (IO_L18P_T2_AD13P_35)
DATA2-8_0: R2492.2, U31.H20 (IO_L17N_T2_AD5N_35)
DATA2-9_0: R2486.2, U31.J19 (IO_L10N_T1_AD11N_35)
DATA2-11_0: R9996.2, U31.K18 (IO_L12N_T1_MRCC_35)
DATA2-13_0: R2488.2, U31.K19 (IO_L10P_T1_AD11P_35)
DATA2-14_0: R2506.2, U31.J20 (IO_L17P_T2_AD5P_35)
DATA2-15_0: R2489.2, U31.L16 (IO_L11P_T1_SRCC_35)
DATA2-16_0: R2505.2, U31.L19 (IO_L9P_T1_DQS_AD3P_35)
DATA2-17_0: R2490.2, U31.M18 (IO_L8N_T1_AD10N_35)
DATA2-18_0: R2507.2, U31.L20 (IO_L9N_T1_DQS_AD3N_35)
DATA2-19_0: R2491.2, U31.M20 (IO_L7N_T1_AD2N_35)
DATA2-20_0: R2504.2, U31.L17 (IO_L11N_T1_SRCC_35)
DATA3-5_0: R2496.2, U31.M19 (IO_L7P_T1_AD2P_35)
DATA3-6_0: R2510.2, U31.N20 (IO_L14P_T2_SRCC_34)
DATA3-7_0: R2497.2, U31.P18 (IO_L23N_T3_34)
DATA3-8_0: R2511.2, U31.M17 (IO_L8P_T1_AD10P_35)
DATA3-9_0: R2498.2, U31.N17 (IO_L23P_T3_34)
DATA3-11_0: R2499.2, U31.P20 (IO_L14N_T2_SRCC_34)
DATA3-13_0: R2500.2, U31.R18 (IO_L20N_T3_34)
DATA3-14_0: R1492.2, U31.R19 (IO_0_34)
DATA3-15_0: R2501.2, U31.P19 (IO_L13N_T2_MRCC_34)
DATA3-16_0: R1491.2, U31.T20 (IO_L15P_T2_DQS_34)
DATA3-17_0: R2502.2, U31.U20 (IO_L15N_T2_DQS_34)
DATA3-18_0: R2509.2, U31.T19 (IO_25_34)
DATA3-19_0: R2503.2, U31.V20 (IO_L16P_T2_34)
DATA3-20_0: R2508.2, U31.U19 (IO_L12N_T1_MRCC_34)
GND: C307.2, C308.2, C310.2, C319.2, C322.2, C323.2, C362.1, C363.1, C364.1, DATA1.3, DATA1.4, DATA1.12, DATA2.3, DATA2.4, DATA2.12, DATA3.3, DATA3.4, DATA3.12, R277.1, R2541.2, X5.4 (GND)
IN: C307.1, C308.1, C310.1, C319.1, C322.1, C323.1, D21.1 (K), D22.1 (K), D23.1 (K)
MDC_0: U31.W15 (IO_L10N_T1_34)
unnamed: C362.2, C364.2, L29.1, X5.2 (Vdd)
unnamed: D21.2 (A), DATA1.1, DATA1.2
unnamed: D22.2 (A), DATA2.1, DATA2.2
unnamed: D23.2 (A), DATA3.1, DATA3.2
unnamed: DATA1.5, R2479.1
unnamed: DATA1.6, R2483.1
unnamed: DATA1.7, R2478.1
unnamed: DATA1.8, R2482.1
unnamed: DATA1.9, R2477.1
unnamed: DATA1.11, R2476.1
unnamed: DATA1.13, R9997.1
unnamed: DATA1.14, R1488.1
unnamed: DATA1.15, R2474.1
unnamed: DATA1.16, R1487.1
unnamed: DATA1.17, R2473.1
unnamed: DATA1.18, R2480.1
unnamed: DATA1.19, R2472.1
unnamed: DATA1.20, R2481.1
unnamed: DATA2.5, R2484.1
unnamed: DATA2.6, R2493.1
unnamed: DATA2.7, R2485.1
unnamed: DATA2.8, R2492.1
unnamed: DATA2.9, R2486.1
unnamed: DATA2.11, R9996.1
unnamed: DATA2.13, R2488.1
unnamed: DATA2.14, R2506.1
unnamed: DATA2.15, R2489.1
unnamed: DATA2.16, R2505.1
unnamed: DATA2.17, R2490.1
unnamed: DATA2.18, R2507.1
unnamed: DATA2.19, R2491.1
unnamed: DATA2.20, R2504.1
unnamed: DATA3.5, R2496.1
unnamed: DATA3.6, R2510.1
unnamed: DATA3.7, R2497.1
unnamed: DATA3.8, R2511.1
unnamed: DATA3.9, R2498.1
unnamed: DATA3.11, R2499.1
unnamed: DATA3.13, R2500.1
unnamed: DATA3.14, R1492.1
unnamed: DATA3.15, R2501.1
unnamed: DATA3.16, R1491.1
unnamed: DATA3.17, R2502.1
unnamed: DATA3.18, R2509.1
unnamed: DATA3.19, R2503.1
unnamed: DATA3.20, R2508.1
unnamed: R277.2, X5.1 (EN)
unnamed: R1372.1, X5.3 (OUT)
unnamed: R1372.2, U31.N18 (IO_L13P_T2_MRCC_34)
unnamed: R2461.2, U31.U15 (IO_L11N_T1_SRCC_34)
unnamed: R2462.2, U31.W19 (IO_L22N_T3_34)
unnamed: R2463.2, U31.W18 (IO_L22P_T3_34)
unnamed: R2464.2, U31.Y18 (IO_L17P_T2_34)
unnamed: R2465.2, U31.V18 (IO_L21N_T3_DQS_34)
unnamed: R2466.2, U31.Y19 (IO_L17N_T2_34)
unnamed: R2540.1, R2541.1, U31.U13 (IO_L3P_T0_DQS_PUDC_B_34)
REST.ON_0: U31.Y14 (IO_L8N_T1_34)
RXCLK_0: U31.U14 (IO_L11P_T1_SRCC_34)
RXD0_0: U31.Y16 (IO_L7P_T1_34)
RXD1_0: U31.V16 (IO_L18P_T2_34)
RXD2_0: U31.V17 (IO_L21P_T3_DQS_34)
RXD3_0: U31.Y17 (IO_L7N_T1_34)
RXDV_0: U31.W16 (IO_L18N_T2_34)
TXCLK_0: R2461.1
TXD0_0: R2463.1
TXD1_0: R2464.1
TXD2_0: R2465.1
TXD3_0: R2466.1
TXEN_0: R2462.1
U3.U12_0: U31.U12 (IO_L2N_T0_34)
U3.V12_0: U31.V12 (IO_L4P_T0_34)
U3.V13_0: U31.V13 (IO_L3N_T0_DQS_34)
U3.V15_0: U31.V15 (IO_L10P_T1_34)
U3.W13_0: U31.W13 (IO_L4N_T0_34)
U3.W14_0: U31.W14 (IO_L8P_T1_34)
U31-L14_0: U31.L14 (IO_L22P_T3_AD7P_35)
U31-N16_0: U31.N16 (IO_L21N_T3_DQS_AD14N_35)
U31.W20_0: U31.W20 (IO_L16N_T2_34)
VCCE: C363.2, L29.2, R2540.2, U31.N19 (VCCO_34), U31.R15 (VCCO_34), U31.T18 (VCCO_34), U31.V14 (VCCO_34), U31.W17 (VCCO_34), U31.Y20 (VCCO_34)
VCCO: U31.C19 (VCCO_35), U31.F18 (VCCO_35), U31.H14 (VCCO_35), U31.J17 (VCCO_35), U31.K20 (VCCO_35), U31.M16 (VCCO_35)
XOUT.0_0: U31.U18 (IO_L12P_T1_MRCC_34)

Notes on the sheet:
Data Conns
Data to Eth Phy
OPTO J5P3 IN
OPTO J3P4 OUT
OPTO J3P3 IN
GRN LED6
OPTO J5P4 OUT
RED LED6
PHY CLK
