xjtuecho/EBAZ4205/HW/ebaz4205/kicad/Zynq_Pwr.kicad_sch

## KiCad design HW/ebaz4205/kicad/Zynq_Pwr.kicad_sch (2021-02-16)

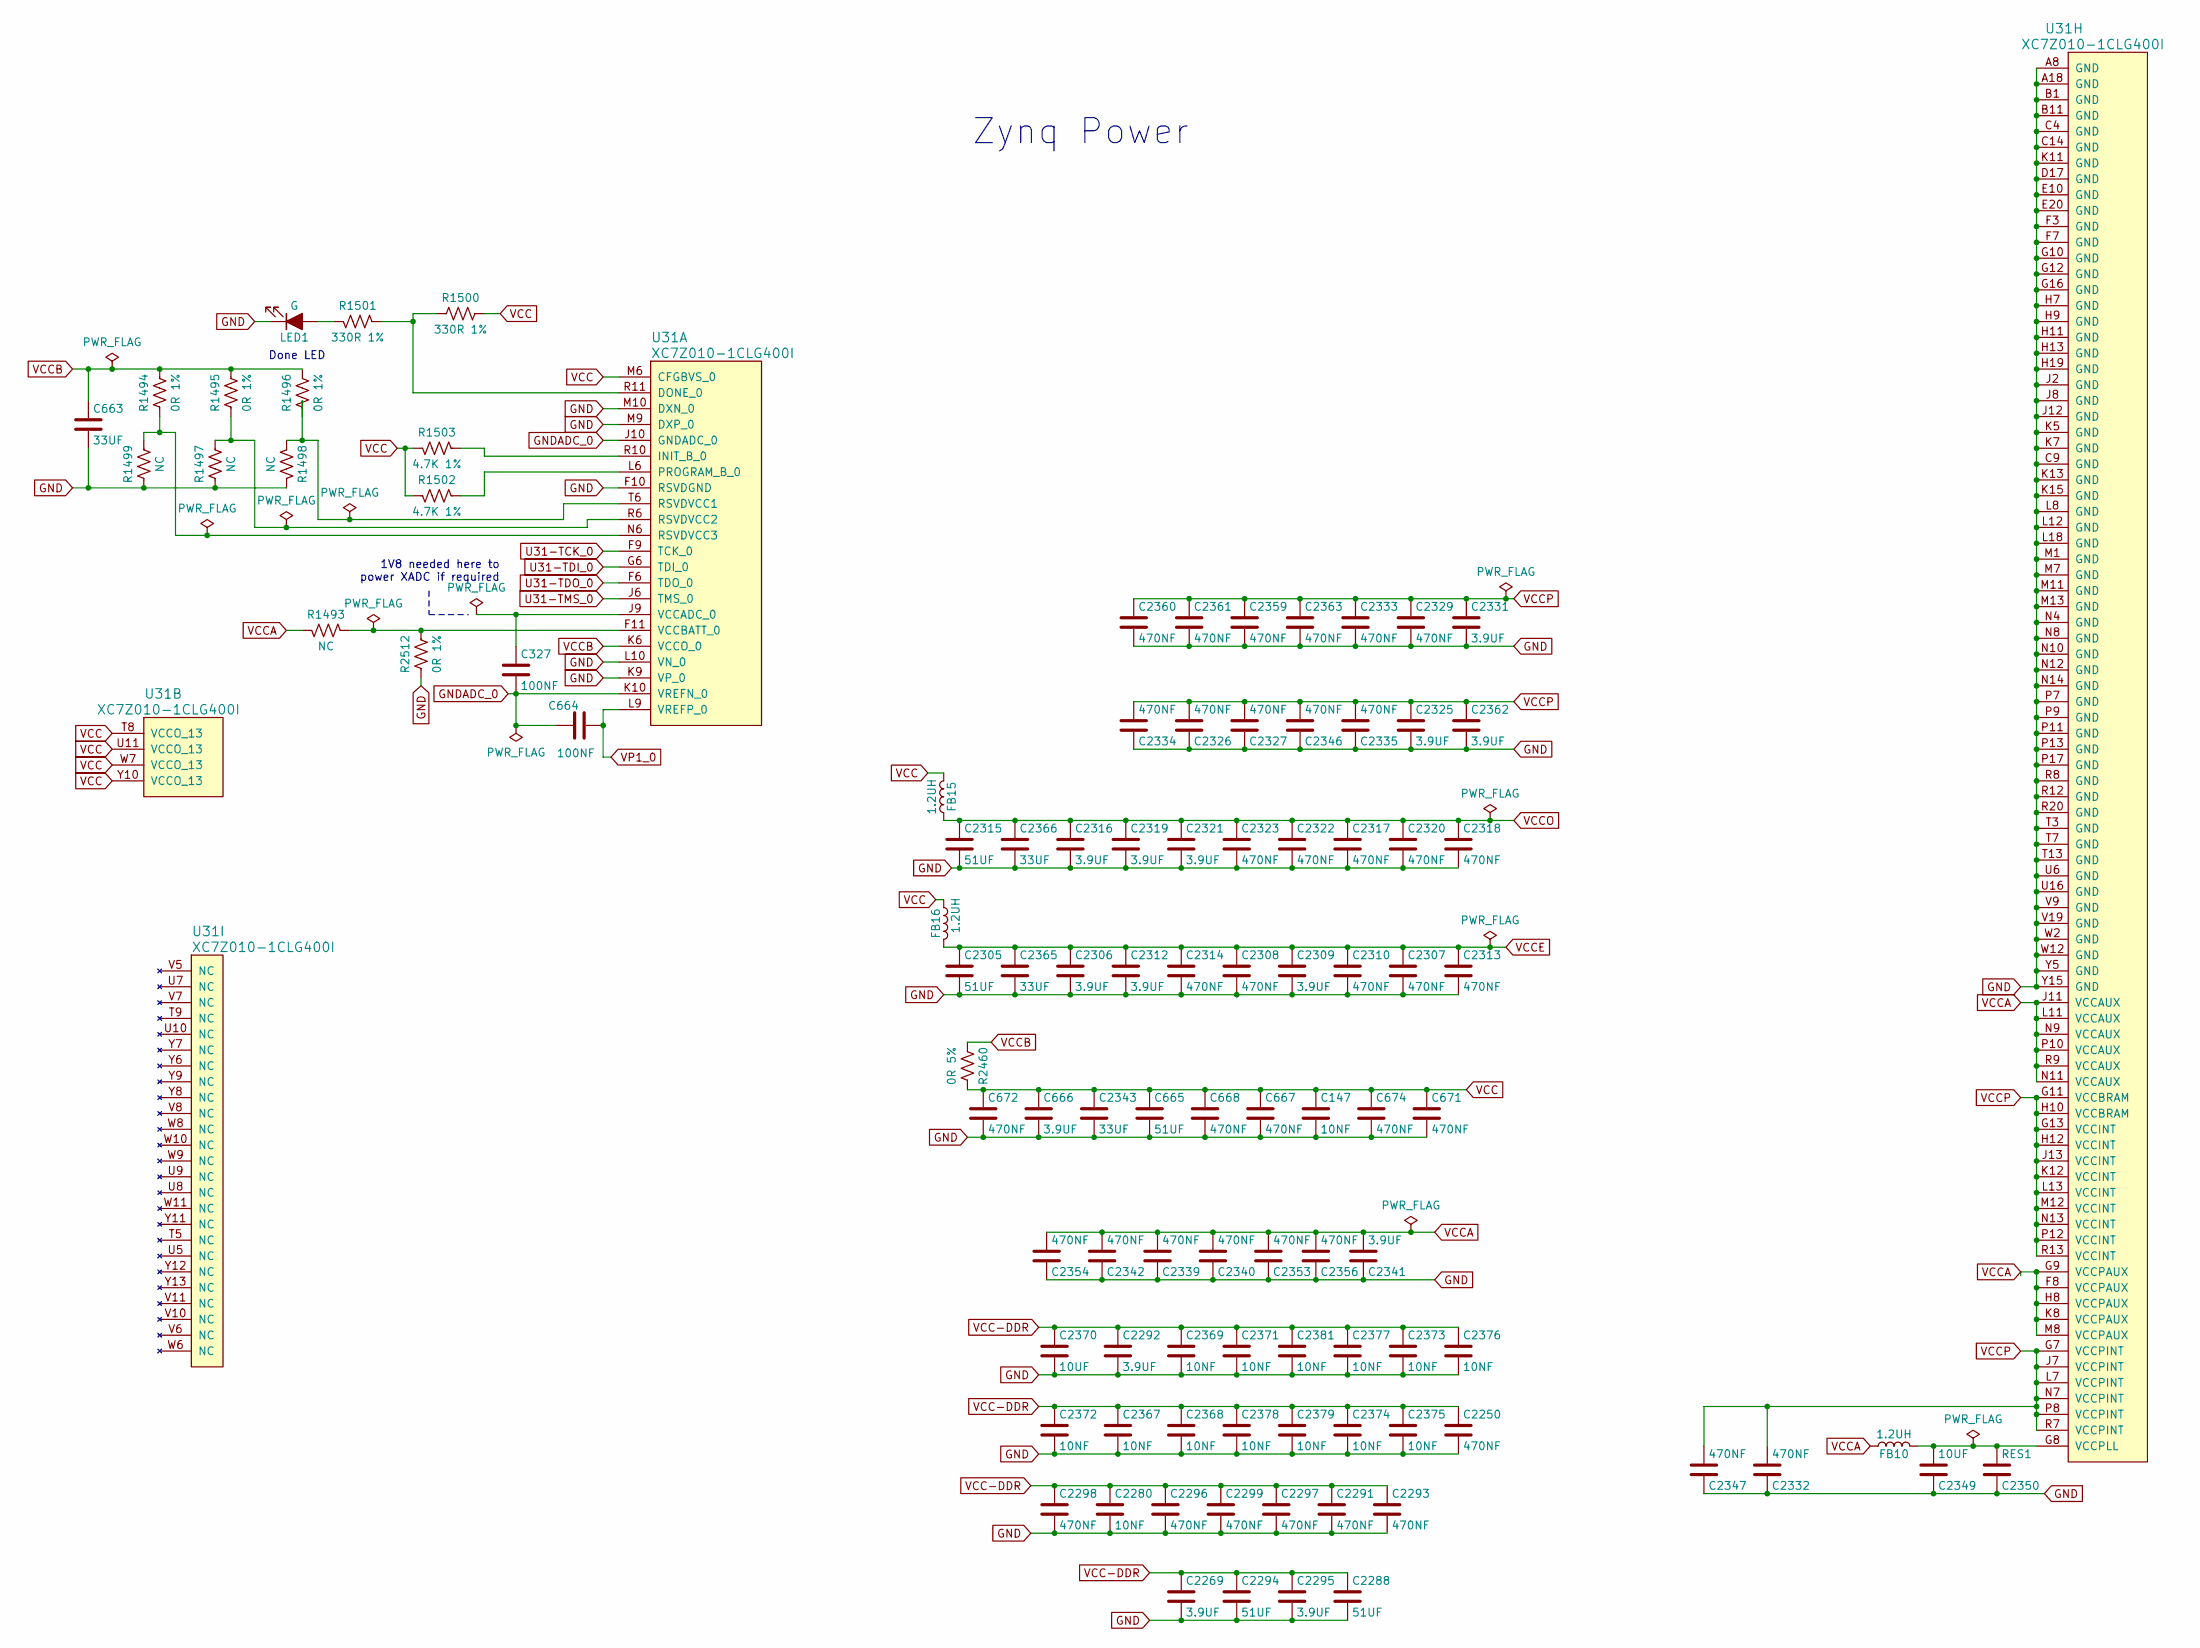
[picture p19: schematic Zynq_Pwr.kicad_sch]

Parts:
C147, C2280, C2367, C2368, C2369, C2371, C2372, C2373, C2374, C2375, C2376, C2377, C2378, C2379, C2381: 10NF
C327, C664: 100NF
C663, C2343, C2365, C2366: 33UF
C665, C2288, C2294, C2305, C2315: 51UF
C666, C2269, C2292, C2295, C2306, C2309, C2312, C2316, C2319, C2321, C2325, C2331, C2341, C2362: 3.9UF
C667, C668, C671, C672, C674, C2250, C2291, C2293, C2296, C2297, C2298, C2299, C2307, C2308, C2310, C2313, C2314, C2317, C2318, C2320, C2322, C2323, C2326, C2327, C2329, C2332, C2333, C2334, C2335, C2339, C2340, C2342, C2346, C2347, C2353, C2354, C2356, C2359, C2360, C2361, C2363: 470NF
C2349, C2370: 10UF
C2350: RES1
FB10, FB15, FB16: 1.2UH
LED1: G
R1493, R1497, R1498, R1499: NC
R1494, R1495, R1496, R2512: 0R 1%
R1500, R1501: 330R 1%
R1502, R1503: 4.7K 1%
R2460: 0R 5%
U31: XC7Z010-1CLG400I

Connections:
GND: C147.2, C663.2, C665.2, C666.1, C667.2, C668.1, C671.1, C672.1, C674.1, C2250.1, C2269.2, C2280.2, C2288.1, C2291.1, C2292.2, C2293.2, C2294.2, C2295.1, C2296.2, C2297.1, C2298.2, C2299.1, C2305.1, C2306.1, C2307.2, C2308.1, C2309.1, C2310.2, C2312.1, C2313.2, C2314.2, C2315.2, C2316.2, C2317.1, C2318.2, C2319.1, C2320.2, C2321.1, C2322.1, C2323.1, C2325.2, C2326.2, C2327.2, C2329.1, C2331.2, C2332.1, C2333.1, C2334.1, C2335.2, C2339.2, C2340.1, C2341.1, C2342.2, C2343.1, C2346.2, C2347.1, C2349.1, C2350.1, C2353.1, C2354.2, C2356.1, C2359.1, C2360.1, C2361.1, C2362.2, C2363.1, C2365.1, C2366.2, C2367.2, C2368.2, C2369.2, C2370.2, C2371.2, C2372.2, C2373.1, C2374.2, C2375.2, C2376.2, C2377.1, C2378.2, C2379.2, C2381.1, LED1.1 (K), R1497.1, R1498.1, R1499.1, R2512.1, U31.A8 (GND), U31.A18 (GND), U31.B1 (GND), U31.B11 (GND), U31.C4 (GND), U31.C9 (GND), U31.C14 (GND), U31.D17 (GND), U31.E10 (GND), U31.E20 (GND), U31.F3 (GND), U31.F7 (GND), U31.F10 (RSVDGND), U31.G10 (GND), U31.G12 (GND), U31.G16 (GND), U31.H7 (GND), U31.H9 (GND), U31.H11 (GND), U31.H13 (GND), U31.H19 (GND), U31.J2 (GND), U31.J8 (GND), U31.J12 (GND), U31.K5 (GND), U31.K7 (GND), U31.K9 (VP_0), U31.K11 (GND), U31.K13 (GND), U31.K15 (GND), U31.L8 (GND), U31.L10 (VN_0), U31.L12 (GND), U31.L18 (GND), U31.M1 (GND), U31.M7 (GND), U31.M9 (DXP_0), U31.M10 (DXN_0), U31.M11 (GND), U31.M13 (GND), U31.N4 (GND), U31.N8 (GND), U31.N10 (GND), U31.N12 (GND), U31.N14 (GND), U31.P7 (GND), U31.P9 (GND), U31.P11 (GND), U31.P13 (GND), U31.P17 (GND), U31.R8 (GND), U31.R12 (GND), U31.R20 (GND), U31.T3 (GND), U31.T7 (GND), U31.T13 (GND), U31.U6 (GND), U31.U16 (GND), U31.V9 (GND), U31.V19 (GND), U31.W2 (GND), U31.W12 (GND), U31.Y5 (GND), U31.Y15 (GND)
GNDADC_0: C327.2, C664.1, U31.J10 (GNDADC_0), U31.K10 (VREFN_0)
unnamed: C327.1, U31.J9 (VCCADC_0)
unnamed: C2349.2, C2350.2, FB10.1, U31.G8 (VCCPLL)
unnamed: LED1.2 (A), R1501.2
unnamed: R1493.1, R2512.2, U31.F11 (VCCBATT_0)
unnamed: R1494.1, R1499.2, U31.N6 (RSVDVCC3)
unnamed: R1495.1, R1497.2, U31.R6 (RSVDVCC2)
unnamed: R1496.1, R1498.2, U31.T6 (RSVDVCC1)
unnamed: R1500.1, R1501.1, U31.R11 (DONE_0)
unnamed: R1502.1, U31.L6 (PROGRAM_B_0)
unnamed: R1503.1, U31.R10 (INIT_B_0)
U31-TCK_0: U31.F9 (TCK_0)
U31-TDI_0: U31.G6 (TDI_0)
U31-TDO_0: U31.F6 (TDO_0)
U31-TMS_0: U31.J6 (TMS_0)
VCC: C147.1, C665.1, C666.2, C667.1, C668.2, C671.2, C672.2, C674.2, C2343.2, FB15.2, FB16.2, R1500.2, R1502.2, R1503.2, R2460.2, U31.M6 (CFGBVS_0), U31.T8 (VCCO_13), U31.U11 (VCCO_13), U31.W7 (VCCO_13), U31.Y10 (VCCO_13)
VCC-DDR: C2250.2, C2269.1, C2280.1, C2288.2, C2291.2, C2292.1, C2293.1, C2294.1, C2295.2, C2296.1, C2297.2, C2298.1, C2299.2, C2367.1, C2368.1, C2369.1, C2370.1, C2371.1, C2372.1, C2373.2, C2374.1, C2375.1, C2376.1, C2377.2, C2378.1, C2379.1, C2381.2
VCCA: C2339.1, C2340.2, C2341.2, C2342.1, C2353.2, C2354.1, C2356.2, FB10.2, R1493.2, U31.F8 (VCCPAUX), U31.G9 (VCCPAUX), U31.H8 (VCCPAUX), U31.J11 (VCCAUX), U31.K8 (VCCPAUX), U31.L11 (VCCAUX), U31.M8 (VCCPAUX), U31.N9 (VCCAUX), U31.N11 (VCCAUX), U31.P10 (VCCAUX), U31.R9 (VCCAUX)
VCCB: C663.1, R1494.2, R1495.2, R1496.2, R2460.1, U31.K6 (VCCO_0)
VCCE: C2305.2, C2306.2, C2307.1, C2308.2, C2309.2, C2310.1, C2312.2, C2313.1, C2314.1, C2365.2, FB16.1
VCCO: C2315.1, C2316.1, C2317.2, C2318.1, C2319.2, C2320.1, C2321.2, C2322.2, C2323.2, C2366.1, FB15.1
VCCP: C2325.1, C2326.1, C2327.1, C2329.2, C2331.1, C2332.2, C2333.2, C2334.2, C2335.1, C2346.1, C2347.2, C2359.2, C2360.2, C2361.2, C2362.1, C2363.2, U31.G7 (VCCPINT), U31.G11 (VCCBRAM), U31.G13 (VCCINT), U31.H10 (VCCBRAM), U31.H12 (VCCINT), U31.J7 (VCCPINT), U31.J13 (VCCINT), U31.K12 (VCCINT), U31.L7 (VCCPINT), U31.L13 (VCCINT), U31.M12 (VCCINT), U31.N7 (VCCPINT), U31.N13 (VCCINT), U31.P8 (VCCPINT), U31.P12 (VCCINT), U31.R7 (VCCPINT), U31.R13 (VCCINT)
VP1_0: C664.2, U31.L9 (VREFP_0)

Notes on the sheet:
Done LED
1V8 needed here to power XADC if required
Zynq Power
