xjtuecho/EBAZ4205/HW/ebaz4205/kicad/ebaz4205.kicad_sch

## KiCad design HW/ebaz4205/kicad/ebaz4205.kicad_sch (2021-02-16)

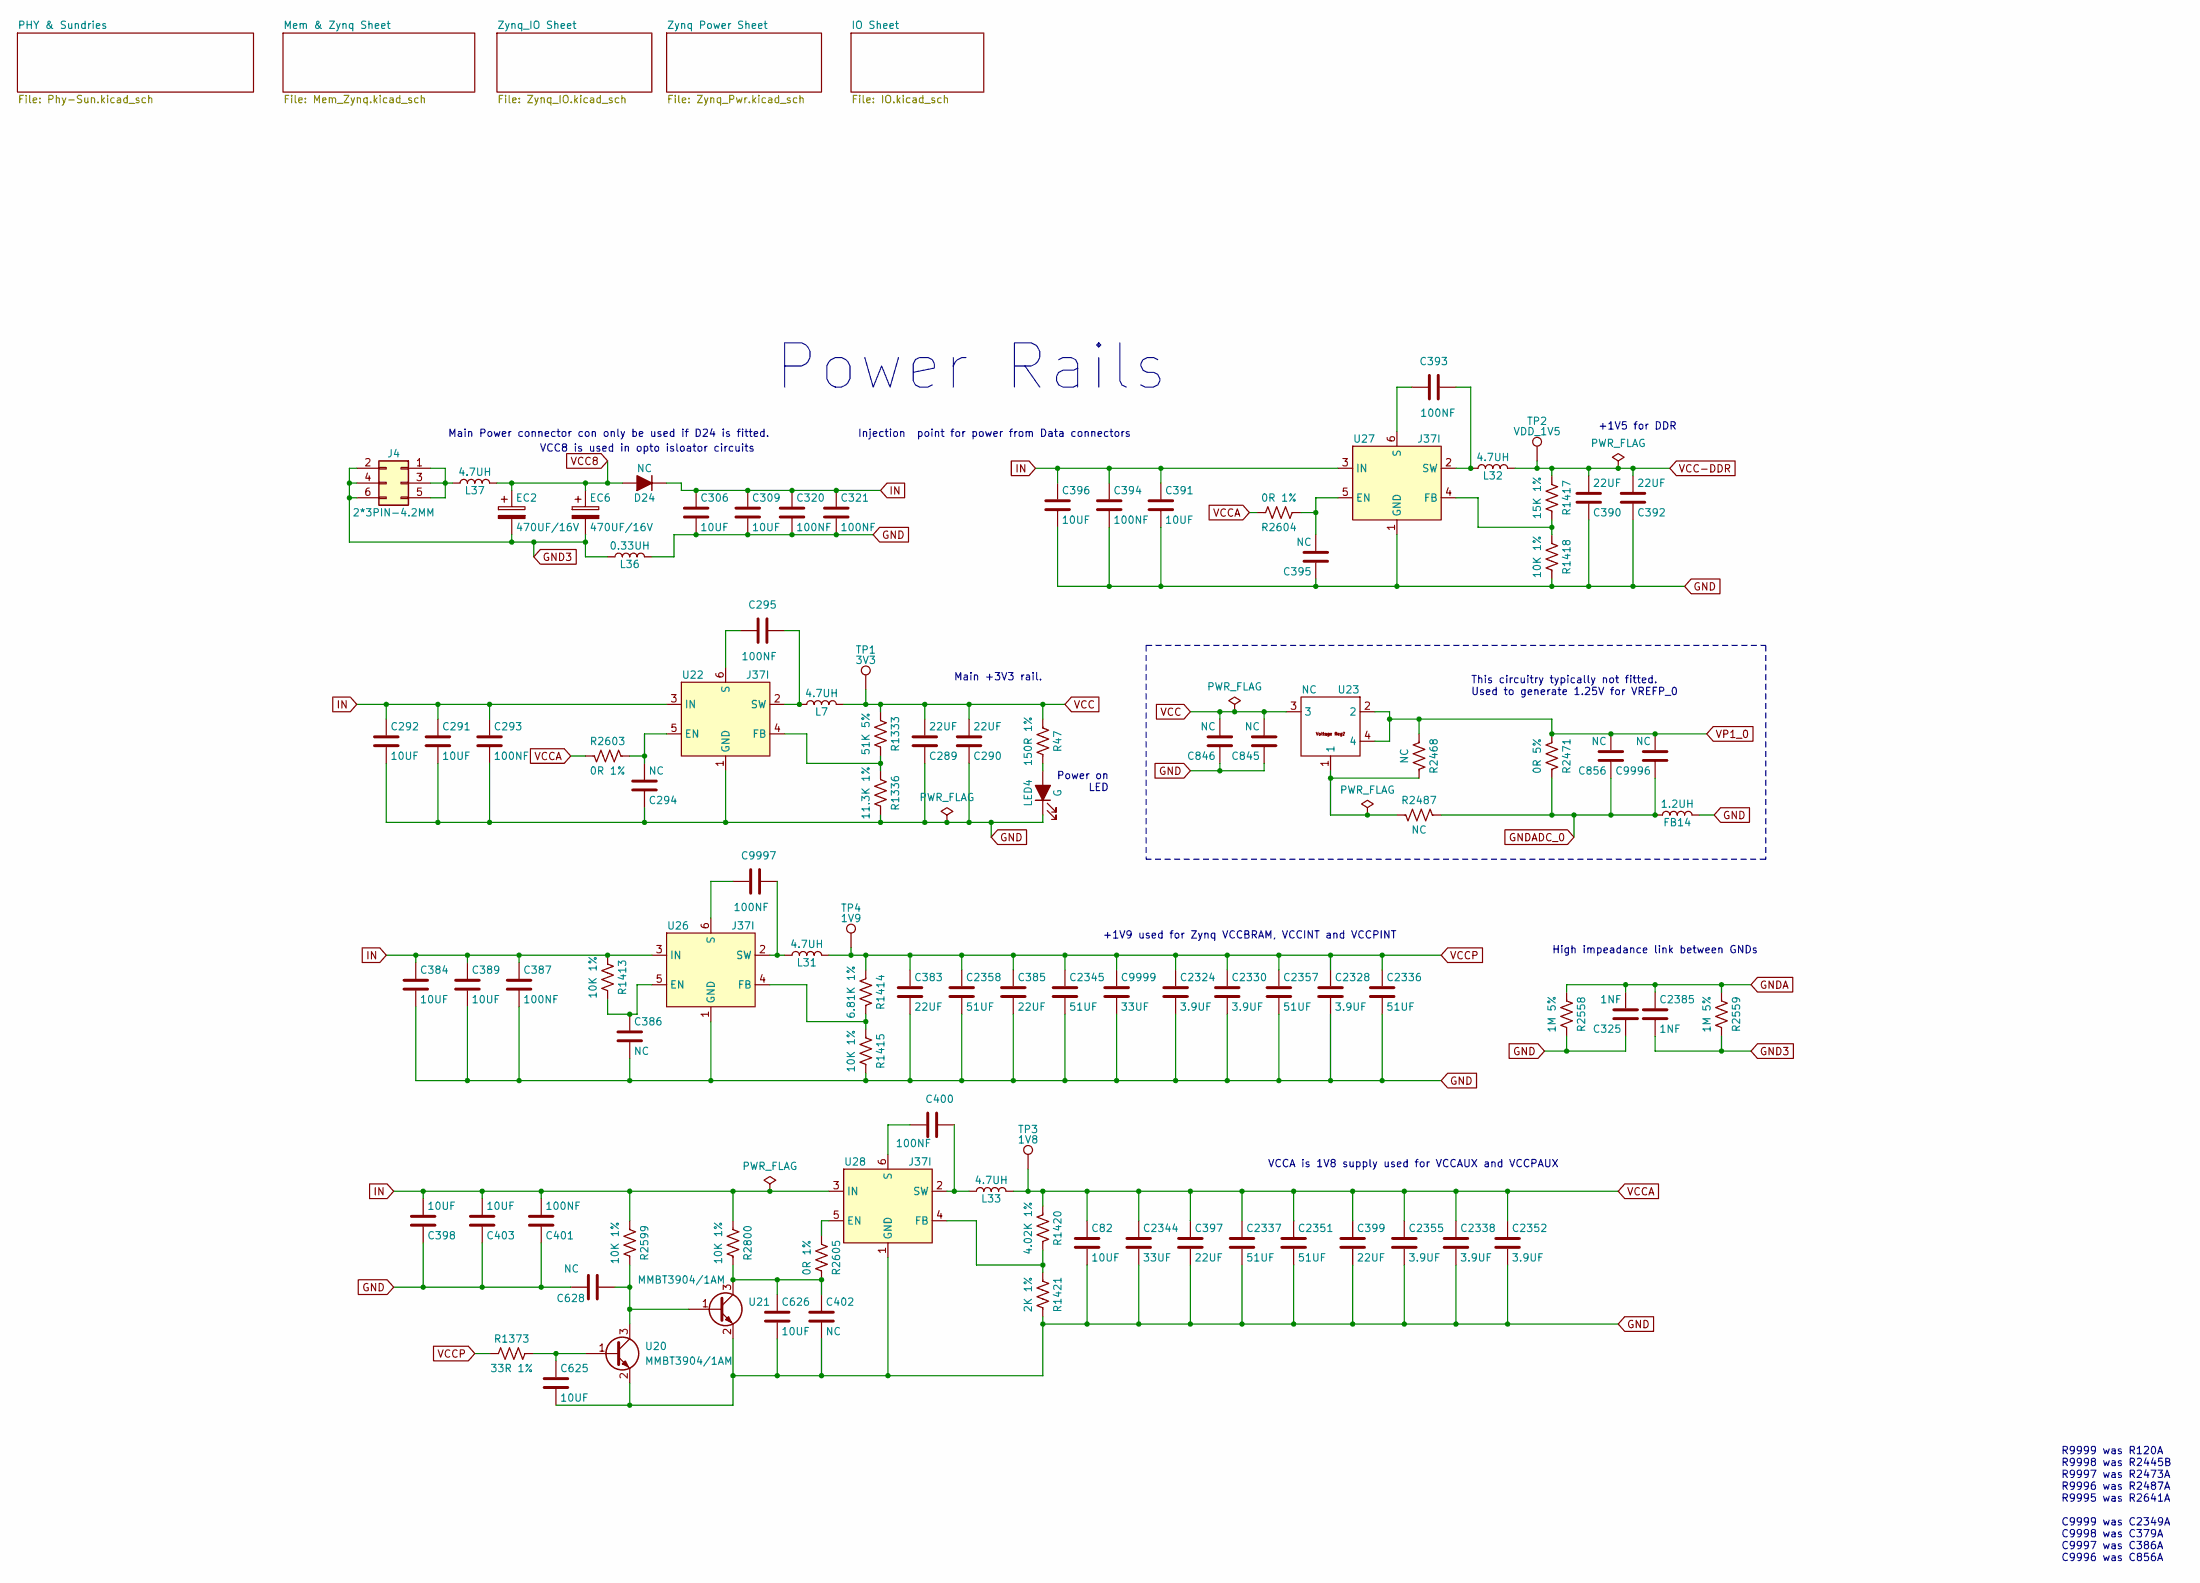
[picture p20: schematic ebaz4205.kicad_sch]

Parts:
C82, C291, C292, C306, C309, C384, C389, C391, C396, C398, C403, C625, C626: 10UF
C289, C290, C383, C385, C390, C392, C397, C399: 22UF
C293, C295, C320, C321, C387, C393, C394, C400, C401, C9997: 100NF
C294, C386, C395, C402, C628, C845, C846, C856, C9996: NC
C325, C2385: 1NF
C2324, C2328, C2330, C2338, C2352, C2355: 3.9UF
C2336, C2337, C2345, C2351, C2357, C2358: 51UF
C2344, C9999: 33UF
D24: NC
EC2, EC6: 470UF/16V
FB14: 1.2UH
J4: 2*3PIN-4.2MM
L7, L31, L32, L33, L37: 4.7UH
L36: 0.33UH
LED4: G
R47: 150R 1%
R1333: 51K 5%
R1336: 11.3K 1%
R1373: 33R 1%
R1413, R1415, R1418, R2599, R2800: 10K 1%
R1414: 6.81K 1%
R1417: 15K 1%
R1420: 4.02K 1%
R1421: 2K 1%
R2468, R2487: NC
R2471: 0R 5%
R2558, R2559: 1M 5%
R2603, R2604, R2605: 0R 1%
TP1: 3V3
TP2: VDD_1V5
TP3: 1V8
TP4: 1V9
U20, U21: MMBT3904/1AM
U22, U26, U27, U28: J37I
U23: NC

Connections:
GND: C82.1, C289.1, C290.1, C291.2, C292.2, C293.1, C294.1, C306.2, C309.2, C320.2, C321.2, C325.1, C383.2, C384.1, C385.2, C386.2, C387.2, C389.1, C390.1, C391.2, C392.1, C394.1, C395.1, C396.2, C397.2, C398.1, C399.2, C401.1, C402.2, C403.1, C625.2, C626.2, C628.2, C845.1, C846.1, C2324.2, C2328.1, C2330.2, C2336.1, C2337.2, C2338.2, C2344.2, C2345.2, C2351.2, C2352.2, C2355.2, C2357.1, C2358.2, C9999.2, FB14.1, L36.2, LED4.1 (K), R1336.2, R1415.2, R1418.2, R1421.2, R2558.2, U20.2 (E), U21.2 (E), U22.1 (GND), U26.1 (GND), U27.1 (GND), U28.1 (GND)
GND3: C2385.2, EC2.2, EC6.2, J4.2, J4.4, J4.6, L36.1, R2559.2
GNDA: C325.2, C2385.1, R2558.1, R2559.1
GNDADC_0: C856.1, C9996.1, FB14.2, R2471.1, R2487.1
IN: C291.1, C292.1, C293.2, C306.1, C309.1, C320.1, C321.1, C384.2, C387.1, C389.2, C391.1, C394.2, C396.1, C398.2, C401.2, C403.2, D24.1 (K), R1413.1, R2599.1, R2800.1, U22.3 (IN), U26.3 (IN), U27.3 (IN), U28.3 (IN)
unnamed: C294.2, R2603.1, U22.5 (EN)
unnamed: C295.1, U22.6 (S)
unnamed: C295.2, L7.2, U22.2 (SW)
unnamed: C386.1, R1413.2, U26.5 (EN)
unnamed: C393.1, U27.6 (S)
unnamed: C393.2, L32.2, U27.2 (SW)
unnamed: C395.2, R2604.1, U27.5 (EN)
unnamed: C400.1, L33.1, U28.2 (SW)
unnamed: C400.2, U28.6 (S)
unnamed: C402.1, C626.1, R2605.2, R2800.2, U21.3 (C)
unnamed: C625.1, R1373.2, U20.1 (B)
unnamed: C628.1, R2599.2, U20.3 (C), U21.1 (B)
unnamed: C9997.1, L31.1, U26.2 (SW)
unnamed: C9997.2, U26.6 (S)
unnamed: J4.1, J4.3, J4.5, L37.1
unnamed: LED4.2 (A), R47.2
unnamed: R1333.2, R1336.1, U22.4 (FB)
unnamed: R1414.1, R1415.1, U26.4 (FB)
unnamed: R1417.2, R1418.1, U27.4 (FB)
unnamed: R1420.1, R1421.1, U28.4 (FB)
unnamed: R2468.1, R2487.2, U23.1
unnamed: R2605.1, U28.5 (EN)
VCC: C289.2, C290.2, C845.2, C846.2, L7.1, R47.1, R1333.1, TP1.1, U23.3
VCC8: D24.2 (A), EC2.1, EC6.1, L37.2
VCC-DDR: C390.2, C392.2, L32.1, R1417.1, TP2.1
VCCA: C82.2, C397.1, C399.1, C2337.1, C2338.1, C2344.1, C2351.1, C2352.1, C2355.1, L33.2, R1420.2, R2603.2, R2604.2, TP3.1
VCCP: C383.1, C385.1, C2324.1, C2328.2, C2330.1, C2336.2, C2345.1, C2357.2, C2358.1, C9999.1, L31.2, R1373.1, R1414.2, TP4.1
VP1_0: C856.2, C9996.2, R2468.2, R2471.2, U23.2, U23.4

Notes on the sheet:
VCC8 is used in opto isloator circuits
Main Power connector con only be used if D24 is fitted.
Power Rails
Main +3V3 rail.
Power on LED
Injection point for power from Data connectors
+1V9 used for Zynq VCCBRAM, VCCINT and VCCPINT
This circuitry typically not fitted. Used to generate 1.25V for VREFP_0
VCCA is 1V8 supply used for VCCAUX and VCCPAUX
+1V5 for DDR
High impeadance link between GNDs
R9999 was R120A R9998 was R2445B R9997 was R2473A R9996 was R2487A R9995 was R2641A C9999 was C2349A C9998 was C379A C9997 was C386A C9996 was C856A
